tomonoriyamazaki/toytalker/docs/qwen3-tts-current-status.md

# ZakiCorp TTS（Qwen3-TTS）調査の経緯（2026-09-12〜13）

元実装の同時要求試験から、言葉の繰り返し・抜けの原因特定、バッチ推論エンジンの実装と本番反映までの経緯を時系列で残す。**現在の状態と設計・計測の詳細は [バッチエンジンの実装と検証](qwen3-tts-batch-engine-2026-09-12.md) を参照。** 本書は「なぜそうなったか」を追うための記録で、「今の結論」以下の各節はその時点の記述のまま残している。

各段階の個別メモ（同時要求結果・処理能力分析・区間計測・CUDAトレース・改善候補比較・可変チャンク・並列比較）は2026-09-13に本書と batch-engine へ要点を統合して削除した。生ログ・音声は `tts-models/faster-qwen3-tts/benchmarks/concurrency/results/`（Git対象外）にある。

## 今の結論

**改善版は1件ずつなら少し速くなり、確認した音声も問題なかった。しかし、4件同時では待ち時間・再生の途切れが残り、言葉の繰り返しや抜けも見つかった。複数人を快適に捌ける状態には、まだできていない。**

改善版は本番に適用していない。検証後に元のプログラム・設定へ戻し、音声生成と監視タスクの復帰を確認済み。現在は調査を停止しており、このまとめの作成中に追加の負荷試験は実行していない。

## 何を目指しているか

ToyTalkerを100人が使えるようにしたい。そのために、自前のRTX 5090＋Qwen3-TTSでどれだけ音声を生成できるか、改善の余地があるかを調べている。

「100人がサービスを利用する」ことと「100件が同時に音声生成を要求する」ことは同じ条件ではない。実際の会話頻度や返答の長さも必要だが、現段階では少人数の同時要求でも問題が残っている。100人対応は未達・未検証。

## ここまで何をしたか

| 段階 | やったこと | 分かったこと |
|---|---|---|
| 元の性能を測定 | 元のプログラムに1・2・4・8・16・32件の要求を同時に送った | 初期試験では1〜16件の総生成量がほぼ一定。要求数を増やすと待ちが長くなり、32件は大半が期限超過 |
| 時間の内訳を調査 | トークン生成・波形変換とCPU/GPUの処理時間を計測 | 最初の区間計測ではトークン生成約81%、波形変換約19%。GPUの性能限界そのものは未確定 |
| 小さな高速化を試行 | 重複トークン除去の変更、波形への変換間隔の調整 | 重複除去の変更は約1%の時間短縮。変換間隔を広げると処理量は増えるが、初回音声が遅くなった |
| 先頭を小さく保つ改善版を試行 | 先頭6チャンクは通常と同じにし、その後の変換間隔を広げた | 単独では処理量約7.2%増、初回音声は約0.079秒遅い。ユーザーが比較音声を聞き、違和感なしと確認 |
| 改善版の同時利用を比較 | 通常版と改善版で同時2件・4件を測った | 同時数を増やしても総生成量は増えず、改善版4件では待ち・模擬再生の途切れが残った。保存音声にも異常の報告あり |

## 元実装の分析で分かったこと（2026-09-12）

- **GPUへの入力は1要求分の形。** `api_server.py` は共有モデルの同期ジェネレーターを呼ぶだけで、推論ワーカーやバッチ受付はない。`talker_graph.py` の入出力バッファは `(1, 1, hidden_size)`。同時HTTP要求を増やしてもGPUへ渡すバッチ数は増えず、1〜16件で総生成倍率が約3.1倍で一定なのはこの構成による。
- **推論がイベントループを塞ぐ。** `generate_pcm()` はasyncジェネレーターだが内側の生成は同期処理。StarletteのStreamingResponseが自動で別スレッドへ移すのは同期Iterableだけで、asyncジェネレーターには適用されない。同時16件でHTTPヘッダー到着p95が29秒、32件で `/health` 無応答になったのはこの経路。バッチ版でHTTP側をQueue受け取りだけにしたのはこのため。
- **却下した案。** モデルを単純に複数スレッドから呼ぶ案は、共有CUDA graphとstatic cacheの状態を分離しないため採らない。複数プロセスで独立モデルを置く案は、GPUの取り合いで遅くなり得るのでVRAMの空きだけを理由に採用しない。1.7Bと0.6Bの比較は品質が許せる場合の別案として保留。
- **処理時間の内訳（単独要求）。** トークン生成81%、波形デコード19%、入力準備0.1%。波形デコードを半分にできても全体は約1.10倍、ゼロという非現実的な仮定でも約1.23倍にしかならず、チャンク調整路線では上限が低いと分かった。モデルが最初のチャンクを返すまで0.150秒に対しHTTPの初回PCM p50は0.743秒で、約0.6秒がAPIの1チャンク保留と同期推論中の通信待ち。バッチ版で初回PCMが0.25秒になったのはこの差が消えたため。
- **100人対応の換算。** 100人が各20秒に1回、約8秒の返答を要求すると約40音声秒/実時間秒が必要。元実装の約3.1倍とは約13倍の差。仮定による感度分析で、実際の利用割合・返答長で変わる。

## 「並列テスト」という説明について

**複数の要求を同時に送る試験は、最初から行っている。今回が初めてではない。**

今回作ったのは、音声への変換回数を減らす改善版。複数人分を効率よくGPUで同時に計算する仕組みを新しく実装したわけではない。

実測で言えるのは「要求数を増やしても、全体の音声生成量が増えていない」ということ。内部が完全な直列処理なのか、途中で交互に動いているのかを、この結果だけで決めつけない。以前の説明では「同時要求の試験」と「並列化の実装」を混同させてしまった。

## 改善版の最新結果

| 条件 | 結果 |
|---|---|
| 単独 | 通常比で処理量約7.2%増。初回音声0.748秒→0.827秒。保存した比較音声はユーザー確認で問題なし |
| 同時2件 | 総生成倍率3.40倍。初回音声p95は2.34秒。10/10受信完了、模擬再生の途切れ0/10 |
| 同時4件 | 総生成倍率3.31倍。初回音声p95は4.05秒。20/20受信完了だが、模擬再生の途切れ20/20。聴取した先頭4音声のうち2つに異常 |

「生成倍率3.40倍」は、実時間1秒あたり合計約3.40秒分の音声を生成できたという意味。対応人数を表す数値ではない。2件から4件へ増やしても、この総量は増えなかった。

模擬再生の途切れは、受信時刻から計算した推定。実機スピーカーの音を直接測った結果ではない。また、受信完了は音声内容の正常性を保証しない。完成WAVを再生しても、通信中の待ち時間や途切れはそのまま再現されない。

## 見つかった音声の問題

対象フォルダ:

```text
C:\Users\exodj\projects\tts-models\faster-qwen3-tts\benchmarks\concurrency\results\20260912T125241_468029Z
```

| ファイル | ユーザーによる確認 |
|---|---|
| `measure-000-00.wav` | 言葉の繰り返し、飛ぶ・抜けるような感じがある |
| `measure-000-01.wav` | 言葉の繰り返し、飛ぶ・抜けるような感じがある |
| `measure-000-02.wav` | 問題なし |
| `measure-000-03.wav` | 問題なし |

00・01について、声の崩れやノイズはないとの報告。症状の正確な位置や、どの語が抜けたかまでは未確認。

**原因は未確定。** 元のプログラムにもある同時生成の問題なのか、今回の改善が原因なのかは分かっていない。共有キャッシュ等への干渉は調査候補だが、原因と断定していない。先頭4音声の結果から全20件の品質や不良率も判断しない。

## 次にすること

まず、保存済みの「通常版・4件同時」の音声を聞き、同じ繰り返し・抜けがあるか比較する。追加の負荷試験やサービス停止は不要。

```text
C:\Users\exodj\projects\tts-models\faster-qwen3-tts\benchmarks\concurrency\results\20260912T125417_081918Z
```

対象は `measure-000-00.wav` 〜 `measure-000-03.wav`。これは原因を絞る手掛かりで、この4つだけで原因が確定するわけではない。

その結果を踏まえて、同時生成中の状態が混ざっていないか、改善部分に問題がないかを調べる。処理量を大きく増やすには、その後に独立した要求状態を持つ推論方式などの比較が必要。これらの追加調査・実装はまだ実行していない。

**今の作業状態：まとめの作成まで完了。負荷試験は停止中。本番は元の設定。次のユーザー作業は、上記の通常版4音声の聴取。**

## 追記（2026-09-12 夜）：原因の特定とバッチ推論の見込み

コードとログの再分析で、繰り返し・抜けの有力原因を特定した。推論グラフのKVキャッシュ（`talker_graph.py` の `StaticCache`）がサーバーに1つしかなく、同時要求が交互に進むたびに `prefill_kv` のリセットと各ステップの書き込みで互いの文脈を上書きする。生成済みトークン・テキスト供給・波形復号は要求ごとに独立しているため、声は崩れず文脈だけが混ざる。可変チャンク改善版の問題ではなく、元の実装の構造。同一文・同一話者の試験では症状が確率的にしか出ないが、本番のように文と話者が異なる要求が重なると露骨に出るはず。改善版4件の「音声総量37%増」は、41文字に54.88秒を生成した1件の暴走が主因。切り替えは送信バッファが約64KB（約1.6秒分）を超えた時点で起きており、チャンク境界ごとではない。

同時要求で総処理量が増えないのも同じ構造（1件分のバッチ固定グラフを時分割）による。

実装前の見込み計測として、talker・予測器・波形デコーダーをバッチNで動かした結果、1ステップはN=1の19.9msに対しN=8で27.9ms、N=16で38.3ms。4ステップ＋復号の見込みで総音声生成倍率はN=4で約10.8倍、N=8で約18.4倍、N=16で約25.2倍（現行約3.1倍）。詳細は [バッチエンジンの実装と検証](qwen3-tts-batch-engine-2026-09-12.md) の「設計の根拠となった事前計測」。

次の順は、(1) 別文・別話者を交互に進める再現試験で相互上書きを確定、(2) 音声認識による本文照合を性能計測へ組み込む、(3) 暫定で生成を1本の推論スレッドへ直列化、(4) 要求ごとに独立KV領域を持つバッチ推論の実装と2/4/8件の実測。本番の共有キャッシュ問題は未対策。

## 追記（2026-09-12 深夜）：バッチ推論エンジンの実装完了

上記(4)を実装し、HTTP経由で検証した（[実装と検証](qwen3-tts-batch-engine-2026-09-12.md)）。同時16件で総音声生成倍率20.95倍・初回PCM p95 0.84秒・模擬再生枯渇0/48（現行は3.12倍・33.6秒・全件枯渇）。同時4件で9.42倍・初回p95 0.42秒。単独でも初回PCMが0.75秒→0.25秒。隠れ状態は元実装とbf16の1〜2ulp以内で一致。別話者8件同時も全件完了。

**本番は未適用（元の `api_server.py` のまま）。** 適用前に、保存音声の聴取、音声認識による本文照合、切断・長時間運用の確認が必要。対象ファイルは `tts-models/faster-qwen3-tts/batch_engine.py`、`api_server_batch.py`。

## 追記（2026-09-13）：本番へ適用

ユーザーが保存音声を聴取し、同一文8件・別話者8件とも問題なしと確認（`measure-000-06` の末尾切れは旧実装にも同じ形で存在する生成側のEOS判定で、並列とは無関係）。ユーザー指示により10:27に本番をバッチ版へ切り替えた。手順と復旧は [起動・復旧](tts-boot-recovery.md) の「APIの版の切り替え」、結果は [実装と検証](qwen3-tts-batch-engine-2026-09-12.md) の本番節を参照。

**今の作業状態：本番はバッチ版（`api_server_batch.py`）で稼働中。ngrok経由の同時1/4/8件・別話者8件は受信成功・枯渇0。次のユーザー作業は、スマホ/ESP32からの実会話で音声を確認すること。**

## 追記（2026-09-13 昼）：第2版を本番反映

ユーザーがアプリで会話を確認（問題なし、速くなった体感）。その後、本番で同時16件・切断試験を確認し、cache長1024・波形復号のCUDA graph・同時32件・長文の文末分割を実装して12:06に本番へ反映した。8001番の測定は同時32件で33.0倍（第1版16件で20.95倍）。詳細は [実装と検証](qwen3-tts-batch-engine-2026-09-12.md) の第2版節。

**今の作業状態：本番は第2版で稼働中。次のユーザー作業は、通常会話と長文の読み上げ（分割境界の聞こえ方）の確認。**

## 詳細記録

- [元実装の1〜32件測定](qwen3-tts-capacity-2026-09-12.md) — バッチ版の改善幅の比較対象
- [バッチエンジンの実装と検証](qwen3-tts-batch-engine-2026-09-12.md) — 現行本番版。事前計測（見込み計測・CUDAトレース・改善候補比較）もここに統合
