tomonoriyamazaki/toytalker/docs/device-audio-investigation-2026-09-11.md

# 2026-09-11 デバイスの音途切れ報告・初回調査

## 調査対象と結論

中島さんからの「デバイスと会話できたが、会話が途切れ途切れになる。Wi-Fi環境は良い」という報告を受け、CloudWatchと対象候補のDynamoDB登録情報を読み取り調査した。設定変更・デプロイ・ファーム変更は行っていない。

報告に近い時間帯に、デバイス `90:da:72:49:ba:e1` の会話要求7回を確認。TTSは **Sakura / zundamon**、LLMは **Google / gemini-2.5-flash**。ElevenLabsの同時実行制限を今回の原因とする根拠はない。

ただし、このIDが中島さんへ渡した実機と一致するかは確認待ち。実機ファームのバージョンも未確認。

1回の返答には、短い先行音声の後、Web検索などで次の音声送信が遅れる区間がある。他の返答はサーバー側では比較的速く音声を送信しており、この1件だけで報告全体の音途切れを説明できない。端末の受信・再生状況はCloudWatchだけでは確認できていない。

## 時刻の整理

- 提供画像 `IMG_1195.PNG` のメッセージ表示は **Today 12:21 AM**。0:30ではなく0:21。
- 撮影日が9/11、表示タイムゾーンが日本時間なら、2026-09-11 00:21 JST。画像の表示だけでは日付・タイムゾーンは確定しない。
- 初回ログ調査範囲: **2026-09-11 00:00〜01:00 JST**（UTC 2026-09-10 15:00〜16:00）。
- 送信者の滞在場所は、受信側画面の時刻からは判断しない。

## 調査したデータ

AWSリージョン: `ap-northeast-1`

CloudWatchロググループ:

- `/aws/lambda/toytalk-api-stream-for-esp32-lambda`
- `/aws/lambda/toytalker-backchannel-for-esp32-lambda`
- `/aws/lambda/toytalk-soniox-stt-lambda`
- `/aws/lambda/toytalker-device-setting-lambda`

DynamoDB: `toytalker-devices` の対象候補1件を取得。デバイスID、名前、作成時刻、最終更新時刻、キャラクターID、ファームバージョン属性に限定。

- `created_at`: 2026-09-06T00:59:44.590Z
- `last_seen`: 2026-09-10T15:17:02.258Z（9/11 00:17:02 JST）
- `character_id`: `default`
- `device_name`: 空欄
- `firmware_version`: 取得結果に属性なし

`last_seen`は今回のデバイス登録APIの時刻と一致する。ローカル実装では登録時や設定更新時にも更新されるため、最終会話時刻や常時接続の生存確認値とは扱わない。

## 観測結果

00:17:02 JSTにデバイス登録API呼び出しと対象IDの設定取得があり、その後、次の7件の本文要求があった。

音声秒数はログのPCMバイト数を、実装前提の24kHz・16bit・mono（48,000 bytes/秒）で換算したもの。実際のスピーカー再生時間を測った値ではなく、端末が挿入する無音も含まない。

| 本文要求開始 JST | Lambda所要時間 | 最初の音声送信ログまで | 音声ブロック数 | 合計音声相当時間 |
|---|---:|---:|---:|---:|
| 00:17:15.236 | 1.939秒 | 1.694秒 | 2 | 3.803秒 |
| 00:17:42.069 | 4.444秒 | 1.183秒 | 2 | 9.608秒 |
| 00:22:12.189 | 1.259秒 | 1.224秒 | 1 | 1.212秒 |
| 00:22:46.301 | 1.481秒 | 1.452秒 | 1 | 2.757秒 |
| 00:23:00.929 | 2.608秒 | 1.139秒 | 3 | 5.458秒 |
| 00:23:19.362 | 1.404秒 | 1.240秒 | 2 | 5.760秒 |
| 00:23:35.049 | 1.446秒 | 1.152秒 | 3 | 8.338秒 |

7件ともPCM生成・送信処理のログとLambdaのEND/REPORTがある。取得範囲に明示的な例外・タイムアウトのログは見つからなかった。ただし、クライアントへ返すエラーが必ずCloudWatchへ出るとは限らないため、END/REPORTだけで全処理成功や端末再生成功を証明しない。

相槌ログには00:23:16.840 JSTに「音が途切れるね」という入力断片がある。報告との関連を示す手掛かりだが、相槌ログ自体にはデバイスIDがなく、時刻による相関である。

Soniox用Lambdaで確認できるのは一時キー発行側の処理。音声認識のWebSocketは端末からSonioxへ直接接続するため、その切断・音声送信間隔をこれらのLambdaログから追うことはできない。

## 音声間の空白候補: 00:17:42の返答

Request ID: `7a68104e-f55d-42df-a706-d03d68bb1220`

| イベント | JST |
|---|---|
| Lambda START | 00:17:42.069 |
| 音声1送信ログ: 58,002 bytes、約1.208秒分 | 00:17:43.252 |
| Web検索開始 | 00:17:43.253 |
| Web検索結果取得 | 00:17:45.192 |
| 音声2送信ログ: 403,164 bytes、約8.399秒分 | 00:17:46.481 |
| Lambda END | 00:17:46.513前後（REPORT所要時間4.444秒） |

先頭音声と次の音声の送信ログ間隔は **3.229秒**。このうち検索要求〜結果取得は **1.939秒**。先頭音声は約1.208秒なので、先頭をすぐに再生する仮定なら、次の音声が出るまで約2.02秒の不足が生じ得る。

これは実測の無音長ではない。相槌、端末の初期バッファ、受信遅延、再生開始時刻で実際の空白は変わる。また3.229秒をすべてTTS待ちと解釈しない。検索・検索後のLLM出力・TTS・送信処理を含む。

検索対象はシアトルの天気だったが、話題から物理的な滞在場所を確定しない。今回取得したログには、所在地を判定できる送信元IP情報は確認できなかった。

## 残る候補と確認方法

| 候補 | 根拠と限界 | 次の確認 |
|---|---|---|
| 短い先行音声の後で検索待ち | 上記1件で送信間隔に不足候補あり | 検索なしの返答でも同じ症状か比較 |
| 文ごとの意図的な間 | ローカルv0.5/v0.6/v0.7には`TTS_SEGMENT_GAP_MS = 400`がある | 実機の版を確認し、文間の間なのか単語途中の音切れなのかを区別。v0.4へ同じ設定を当てはめない |
| 端末受信・再生バッファの枯渇 | サーバーが早く送れている返答でも、ネットワークや端末処理による遅れは残り得る | `[PLAYER] underrun`、`[STATS] underruns`、受信・I2Sログ。Wi-Fi電波が良いだけでは通信経路全体の安定性は分からない |
| 音声認識や発話区切りの問題 | 「会話が途切れる」が返答音声だけを指すか未確定 | 入力認識の途切れと出力再生の途切れを区別 |
| 実機ファーム固有の問題 | 実機の版が不明 | 配布時の版・設定を確認。手元のv0.7のAEC等を原因と決めつけない |

端末の再生ログは現在確認したCloudWatchデータには含まれない。シリアルログ取得が難しい場合は、まず短い録画で「文と文の間」「単語の途中」「返答までの待ち」のどれかを切り分ける。その後、必要なら遠隔診断データの送信を別の実装として検討する。

## 次に進む順序

1. 対象IDが中島さんの端末と一致するか、配布ファームの版を確認する。
2. 検索なし・短い返答で症状が出るかを確認する。
3. 端末の受信・バッファ枯渇・再生時刻と、CloudWatchのRequest ID/時刻を対応づける。
4. 原因の所在を絞ってから、文間の間、検索時の応答設計、バッファや送信方式の変更を検討する。

## DynamoDB会話履歴との照合（同日追記）

ユーザーから追加依頼を受け、現在の`owner_id`と対象デバイスIDの組み合わせをパーティションキーとして`toytalker-chat-logs`をQueryした。期間はUTC 2026-09-10 14:00〜16:00（JST 23:00〜翌01:00）。14レコードを評価し、14レコードが該当した。すべて`source=esp`、セッション`1280-470114`の7往復。現在の所有者との組み合わせについての結果であり、過去の別所有者に紐づく履歴まで調べたものではない。

### ユーザー入力の記録

以下は保存された音声認識テキスト。元の発声音声との照合はできておらず、不自然な文字列を本人の発言どおりと断定しない。

| JST | 保存されたユーザー入力 |
|---|---|
| 00:17:15.260 | こんにちは。 |
| 00:17:42.073 | えっと、今日のシアトルの天気を調べたい。 |
| 00:22:12.192 | ズームに行くか、頑張って。 |
| 00:22:46.305 | こちらよくある質問なんですけど。 |
| 00:23:00.931 | これが枕に入れるデバイスで、 |
| 00:23:19.365 | 音が途切れるね。 |
| 00:23:35.052 | キロッパ |

「枕に入れるデバイス」「音が途切れるね」が対象デバイスの本文履歴にもあるため、相槌ログの時刻相関だけだった初回調査より、報告との対応が強まった。氏名による本人確認には至っていない。

00:23:00の入力に対する返答は「枕に入れるデバイスですね！面白そう！それは何をするものなのですか？」。00:23:19の入力に対しては「ごめんなさい、音が途切れてしまいましたか。もう一度お話しいただけますか？」と返答している。後者はユーザー入力に応じたLLMの発言で、システムが音切れを検出した診断ログではない。

### 保存テキストの重複と実際の音声送信の違い

天気の返答はDynamoDB上で「調べてみるね。調べてみるね。」と先頭が重複している。しかし、CloudWatchの音声送信ログは次の2ブロックのみ。

1. 「調べてみるね。」
2. 天気の回答本文

ローカル実装の`emitSegment`には直前の同一文を再送しない処理があり、このログと整合する。**履歴の重複は確認できるが、同じ音声を2回再生した証拠ではない。** テキストの保存経路と音声化経路の差を、別の課題として扱う。

### 設定・利用集計

- 現在のデバイス設定は`character_id=default`。当時のCloudWatchには`hasPersonality=false`があり、独自の人格設定を読み込んだ形跡はない。一般的なシステムプロンプトがないという意味ではない。
- 取得したデバイスレコードには`backchannel_enabled`属性がない。ローカルのキー発行実装では未指定時は有効扱い。実際に同時間帯の相槌生成も観測されている。
- `owner_id`はアプリが生成・保持する`u_`付きUUID。確認したアプリ実装では氏名から生成するIDではなく、取得レコードにも氏名・所在地はない。この値だけで本人や滞在地を特定できない。
- 対象端末の9月利用集計にはUTC日付9/10のLLM/STT/TTSレコードが各1件あり、各`requests=7`。本文TTS文字数は208文字。これは利用集計の加算回数であり、TTSの実HTTPリクエスト数7件という意味ではない。CloudWatchの本文音声ブロックは合計14件。
- 記録上の合計金額は約0.8296円（LLM約0.6640円、STT約0.0720円、TTS約0.0936円）。内部設定のマージン1.5等を含む計算値であり、プロバイダー請求額・AWS費用・相槌も含めた総原価としては使わない。今回、料金設定の妥当性は検証していない。

登録時刻9/6は既存レコードの作成時刻。9/11の登録処理では所有者が更新され得るため、9/6から同じ人が使用していたとは断定しない。

参照: [所有者ID生成](../app/hooks/useOwnerId.ts)、[会話履歴保存・利用集計](../backend/toytalk-api-stream-for-esp32-lambda/index.mjs)

## 手元端末ba:e5との比較（同日10:13〜10:14 JST）

ユーザーが手元の端末で試し「全く問題なく動いた」と報告。CloudWatchで`90:da:72:49:ba:e5`の4要求を確認し、DynamoDBの同一セッション`1471-645527`の4往復と照合した。履歴にも「まあ、特に問題ないように見えますね。」という入力がある。

### 条件の比較

| 項目 | ba:e1（報告対象候補） | ba:e5（手元） |
|---|---|---|
| 観測時間 JST | 00:17〜00:23 | 10:13〜10:14 |
| 使用Lambda | ESP32用本文Lambda | 同じ |
| TTS / voice | Sakura / zundamon | 同じ |
| LLM | Google / gemini-2.5-flash | 同じ |
| キャラクター | default、人格設定なし | ユーザー作成キャラ、人格設定あり |
| 相槌 | 同時間帯に生成あり | 同時間帯に生成あり |
| デバイス名 | 空欄 | v0.2 大スピーカー |
| ファームバージョン属性 | なし | なし |
| 再生状態 | 途切れるとの報告候補 | 問題なしとのユーザー報告 |

**「v0.2 大スピーカー」は登録名であり、実機ファームがv0.2であることの証明ではない。** 両端末の実際のファーム・基板・音響配置・通信環境が同一かは未確認。

本文Lambdaの取得時点の`LastModified`は2026-09-10T10:16:47Z（JST 19:16:47）で、両方の観測時刻より前。間のLambda更新で今回の差が出たことを示す情報はない。現在のコードハッシュは`nmsHU9spd2U08fsJ4fg20/MWAuvjpnCJLMbZ3F2r+Ks=`。設定テーブルや外部サービスの時間帯による変化まで同じと証明したものではない。

### 手元の4要求

| 開始 JST | 内容の概要 | Lambda所要時間 | 最初の音声送信まで | ブロック数 | 音声相当時間 |
|---|---|---:|---:|---:|---:|
| 10:13:54.439 | 声が聞こえるか確認 | 1.694秒 | 1.484秒 | 2 | 2.353秒 |
| 10:14:07.118 | シアトルの天気 | 5.575秒 | 1.891秒 | 2 | 6.258秒 |
| 10:14:33.715 | 問題ないとの発話 | 1.473秒 | 1.301秒 | 2 | 4.931秒 |
| 10:14:43.982 | 東京の天気 | 4.955秒 | 1.215秒 | 3 | 10.629秒 |

時刻・所要時間はCloudWatchのSTART、音声送信ログ、REPORTに基づく。DynamoDBの`duration_ms`とは計測範囲が少し異なるため混ぜて集計しない。端末への到着・再生時刻ではない。

### 同じシアトル天気検索の比較

| 指標 | ba:e1 | ba:e5 |
|---|---:|---:|
| Lambda全体 | 4.444秒 | 5.575秒 |
| 最初の音声送信まで | 1.183秒 | 1.891秒 |
| 最初の音声の長さ相当 | 1.208秒 | 1.327秒 |
| 音声1→音声2の送信ログ間隔 | 3.229秒 | 3.655秒 |
| Web検索時間 | 1.939秒 | 1.674秒 |

ba:e5のRequest ID: `005246ed-712d-4458-ab0d-0389c7c1291e`。

**問題なく聞けた手元のほうが、サーバー全体時間も音声ブロック間隔も長い。** よって「ba:e1だけLambdaが遅かった」という説明はこの比較からは支持されない。短い先行音声の後に検索待ちがあること自体は両方で観測されるため、ba:e1固有の症状の原因と確定しない。

同じ話題でも人格設定・返答の長さ・時刻が異なるため、完全な同条件試験ではない。手元で問題なく聞けた理由を、バッファ量やネットワークだけに決めつけない。次は以下を優先する。

1. 相手の「途切れる」が検索待ち・文間の間・単語途中の音切れのどれかを確認。
2. 配布したファームと手元ファームの版・再生設定を照合。
3. 可能なら同じdefaultキャラクター、ずんだもん、検索なしの短い質問で比較。
4. 端末の受信・アンダーラン記録を取得し、CloudWatchの送信ログと突き合わせる。

手元の天気履歴にも前置きの重複があるが、音声送信では1回のみ。これはba:e1固有の問題ではない。

## 実装参照（一覧）

- [本文Lambda](../backend/toytalk-api-stream-for-esp32-lambda/index.mjs): `ttsBufferSakura`、`sendPCM`、`emitSegment`、Web検索処理
- [デバイス設定Lambda](../backend/toytalker-device-setting-lambda/index.mjs): デバイス登録・`last_seen`更新
- [Sonioxキー発行Lambda](../backend/toytalk-soniox-stt-lambda/index.mjs)
- [v0.5再生終了の既存調査](esp32-playback-end-timing.md)
- [v0.7本文開始の高速化で保留した候補](deferred-items.md)

実装に関する説明はローカルソースを参照。本番コードのダウンロード・差分照合は未実施。
