tomonoriyamazaki/toytalker/docs/esp32-v07-aec.md

# v0.7 AEC音声介入実験版（2026-09-10）

AECの変更を独立して検証し、音量方式へ戻せるよう、Arduinoスケッチをバージョンごとに保持する。

19:02の本文開始ログを受けた高速化候補のうち保留した分は [先送り項目](deferred-items.md) を参照。保存点 `d3a59a8` を基準に、相槌の前置き重複を減らす通知修正だけを実装した。相槌取得の並行化と本文プリバッファの変更は行っていない。

## 最新状況（2026-09-10、20:09以降の追加試験を反映）

- ユーザーが現状を次の開発の基準として受け入れ、`9925fe0` までをローカル `main` へ統合するよう依頼。ほかの改修は統合後の `main` から進められる。以下の配置依存や未確認項目は既知の制約として残し、今回のマージを追加試験待ちにはしない。
- 声による停止・通常再生・本文開始速度は改善報告あり。ただし、未固定のスピーカーをマイクへ向けると意図しない停止が起きることをユーザーが確認した。机上・手持ち静止・再生途中の持ち上げ自体は、今回の比較では問題なし。
- AECを追加調整する場合は、スピーカーとマイクを実際に使う位置・向きに固定して評価する。AECの再適応中だけの問題か、向けた状態でも消し残るのかは未確認。詳細は末尾寄りの「スピーカーの向きを変えた追加試験」を参照。
- AECは自動停止ON、毎ターン再初期化ON、NLP強度NORMAL。抑制強度・参照の整列・割り込み条件の調整余地はあるが、追加試験後の設定変更はしていない。強く抑えるほど人の声も弱め得るため、声への反応と誤停止を両方比較する。
- AECの保存点は `d3a59a8`。その後の②相槌通知修正はビルド済みで、今回の引き継ぎ記録と合わせて保存する。実機の通知値と効果の対応は確認途中。①相槌取得と本文要求の並行化は保留、③本文プリバッファ32KBは維持。ユーザーが別途変更したLambdaプロンプトは `87035d8` でコミット済み。保存内容・コミット名は [CLAUDE.mdの引き継ぎ記録](../CLAUDE.md) を参照し、再開時の状態は `git status` / `git log` で確認する。
- スマホから音声割り込み・相槌を再起動なしでON/OFFする案も相談した。まだ未実装で、今のファームが会話中に設定を同期するわけではない。[現状と設定同期の候補](esp32-ota-settings-plan.md) を参照。

| バージョン | 役割 | 現在の状態 |
| --- | --- | --- |
| [v0.5](../devices/mcu/esp32_s3/toytalker_mini_v0.5/toytalker_mini_v0.5.ino) | 安定版 | 従来の会話・ボタン割り込み。変更しない |
| [v0.6](../devices/mcu/esp32_s3/toytalker_mini_v0.6/toytalker_mini_v0.6.ino) | 音量方式の検証版 | 再生中のマイク監視と音量集計あり。自動停止OFF。調整余地を残す |
| [v0.7](../devices/mcu/esp32_s3/toytalker_mini_v0.7/toytalker_mini_v0.7.ino) | AECの開発版 | 毎ターン再初期化後に改善報告。追加試験では持ち上げ自体は問題なく、未固定スピーカーをマイクへ向けると停止。配置を固定して残る問題を評価する。本文の相槌通知修正も実機評価中 |

## 引き継いだ状態

v0.7の作成時はv0.6のスケッチと4つのヘッダーを独立したファイルとして複製した。Arduino IDEの個人設定はコピーしていない。v0.7からv0.6のヘッダーを参照しないので、AEC開発でv0.6の動作が変わることを避けられる。

- `VOICE_BARGE_DETECT_ONLY=true`。AEC未使用・初期化失敗時の生マイクは音量検出ログのみで、自動停止しない。AECの停止設定は別の `AEC_BARGE_DETECT_ONLY`。
- 生マイク比較用のRMS閾値3,200、保持120ms、ウォームアップ500msを継承。AEC処理後の判定には別の閾値・保持時間を使う。
- `VoiceRxTestMode::MonitorResetEachTurn`。再生中もマイクを動かし、再生後にRXを解放、次の録音で再確保する。
- TTSセグメント間400ms、受信処理、音量・メモリ・切替時間の計測、ボタン割り込みを継承。
- 現時点の起動表示は `ToyTalker Mini v0.7 (AEC barge-in trial)`。初期化に成功した場合だけ `[AEC] ready=1` が出る。

v0.6の10ターン連続会話、音量方式での検出→録音復帰69ms / 36ms、再生音による誤停止等は [v0.6の実機記録](esp32-v06-voice-barge-in.md) にある。これらはv0.7やAECを実機確認した結果ではない。

## 今回の実装

`AecMonitor.h` の `AEC_ENABLED=true`。Espressifの `AEC_MODE_FD_LOW_COST` / NLP `NORMAL` / filter length 4を使用する。モデル用パーティションは追加していない。AEC後のRMSを自動停止の条件に使う。AEC後の音声をSonioxへ送る実装や、停止前の発声を録音へ引き継ぐ実装はまだない。停止後は通常STTに戻り、ボタンでの停止も継続する。

### 再生参照とI2S

v0.7のみ `driver/i2s.h` のlegacy APIから、同じインストール済みコアの `driver/i2s_std.h` へ変更した。新旧ドライバは混在させない。ネットワーク到着時やDMAコピー時のPCMではなく、TXの `on_sent` callbackで、送信を終えたDMAバッファを取り出すための変更。

- マイク: I2S0、16kHz、32bit、左slot、RX DMA 4×512。再生後のRX解放・次回STTでの再確保を継続。
- 再生: I2S1、24kHz、stereo 16bit、TX DMA 8×1023。従来の実サイズ4092 bytesを明示した。ピン、再生音量、区切り400msは継承。
- TXは `auto_clear_after_cb=true` / `auto_clear_before_cb=false`。ゲイン・クリップ後の送信波形をクリア前に取得し、再生データが来ない区間はクリアされた無音も取得する。相槌・本文・区切り無音・末尾flushが同じ経路になる。
- RXの `on_recv` とTXの `on_sent` でDMA完了時刻を記録。これはデジタル転送の完了時刻であり、スピーカーの音響遅延を直接測っているわけではない。
- 従来の `[DMA_TAIL]` は新APIのDMAサイズ・キュー溢れカウンターへ接続した。ドライバ変更後の実機での終了時間は再確認する。

### 参照の整列と評価

参照には24kHzの25タップローパスフィルター（7kHz cutoff）をかけてから、16kHzのマイク時刻へ線形補間する。フィルターの0.5msの群遅延を参照時刻に反映する。DMAサンプル数に沿った時計を使い、IRQ時刻の揺れへ毎フレーム追従せず、小さく補正する。連番欠落や3msを超える時刻差は不連続として扱う。

`AEC_REFERENCE_ADVANCE_MS=16` は、参照をマイクより先の時刻から与えてAECフィルターに因果的な余裕を持たせる試験値。物理的なエコー遅延の実測値ではない。必要な最後の参照サンプル（補間相手を含む）が到着したら、512 samples / 32msのマイクフレームを処理する。未到着なら最大96ms待つ。処理前に全512サンプルを検証し、参照が不足・欠落・上書き済みならそのフレームを評価せず、連続音量窓も切る。参照不足を無音として成功扱いにはしない。

初版は一律96ms待っていたが、01:36の実機結果を受けて到着時点で処理できるよう変更した。起動ログは `max_ref_wait_ms=96`。実際の待ち時間はDMA完了・参照時刻・タスク実行タイミングに依存する。最初の非ゼロTX波形が届く前は検出が未有効なのでAEC演算を省き、接続・受信へCPU時間を残す。**再生終了→STT再開時は保留音声を捨て、その消化を待たない。** 処理中の1フレームとタスク停止通知を待つ時間は残る。未処理の末尾はサマリに含まれず、`held_discarded` に保留枚数を出す。

マイクはSPH0645のDCを除去して16bitへ飽和変換する。v0.6の20msごとの分散RMSと厳密に同じ尺度ではない。AEC用の持続値は32ms×4枚=128msの窓で、v0.6の120ms値からそのまま閾値を移さない。各ターンの参照履歴・時計・音量統計は初期化し、最初の再生音から500msは統計のウォームアップにする。AEC本体は従来起動時に一度確保して再利用していたが、18:26の結果を受け、現在は `AEC_RESET_EACH_TURN=true` で2ターン目以降に本体だけを破棄・再作成する比較版。初回は起動時の未使用インスタンスを使う。小さな受渡しキュー・参照履歴・PCM作業バッファは再利用する。

### メモリと失敗時

インストール済みSDKは `CONFIG_I2S_ISR_IRAM_SAFE=1`。ISRの小さな受渡しキューは内部SRAMに置き、履歴・遅延マイク音声はPSRAMに置く。ISR内でPSRAM、音声処理、ヒープ確保、ログ出力へ触れない。ISRとタスクの共有カウンターは短いESP-IDF critical sectionで保護し、データのコピー中はロックしない。このツールチェーンの `std::atomic<uint32_t>` は常時lock-freeではないため、ISRでは使わない。

AECの状態領域はPSRAMを指定し、APIへ渡す3つの512-sampleバッファは16-byte境界の内部RAM。監視タスクのスタックは4KB→8KB。ISR受渡しを含む `aecMonitor` は約8.4KBの静的内部RAMを使用する。静的RAMのビルド表示と、AEC内部の実行時確保・TLS等の動的確保は別々に評価する。

AEC初期化やバッファ確保に失敗した場合は確保分を解放し、音量計測だけへ戻る。その場合も自動停止はOFF。再生タスクの確保失敗も検出し、リングを使用せず直接再生へ戻る。TLSアロケーターは計測版ではコア標準だったが、01:20の接続失敗を受け、現在は以下のPSRAM固定に変更した。

### TLS作業メモリのPSRAM移行

`TlsMemory.h` の `TLS_PSRAM_ENABLED=true`。起動時、WiFi接続・HTTPS・WSS・AEC初期化より前に一度だけ `mbedtls_platform_set_calloc_free()` を設定し、mbedTLSのcallocを `MALLOC_CAP_SPIRAM | MALLOC_CAP_8BIT` へ固定する。Lambda・Soniox・相槌HTTPSに共通で効く。設定は接続中に変更せず、PSRAM確保失敗時に内部RAMへは戻さない。サイズの乗算オーバーフローを拒否し、freeは元の内部RAM割り当ても扱える `heap_caps_free()` を使う。DMA・ISR・タスクスタックの確保先は変更していない。

Arduino 3.3.11 / IDF 5.5.5のローカルSDKで `CONFIG_MBEDTLS_INTERNAL_MEM_ALLOC=1`、`MBEDTLS_PLATFORM_MEMORY`、実行時アロケーター設定APIを確認した。[Espressifの実装](https://github.com/espressif/esp-idf/blob/v5.5.5/components/mbedtls/port/esp_mem.c) も、内部RAM指定とPSRAM指定のcallocを別の構成として持つ。スケッチ内でSDK設定マクロを書き換える方式は使わない。

起動時にmbedTLS公開callocで20,000 bytesを確保し、外部RAMであることと全ゼロを検査して解放する。`[TLS_MEM] allocator=psram ready=1 ... external=1 zeroed=1` が成功ログ。PSRAMがない・API設定失敗・プローブ不一致なら、アンプOFFでネットワーク接続前に起動を止める。`[BUILD] arduino=... idf=...` も記録する。

`[TLS_MEM]` の `calls / fail / largest_req` は起動プローブを含む累積確保呼び出し数・失敗数・最大要求。現在の使用バイト数ではない。`psram_free / psram_max_blk` と内部RAMの `[HEAP_CHECK]` を同じ接続段階で比較する。前回よりRAMが減っただけでリークと断定しない。音声リングとAECとTLSがPSRAMを共有するので、実機で連続会話・接続時間・音切れ・AECの欠落も確認する。

APIの出発点は [Espressif公式AEC](https://docs.espressif.com/projects/esp-sr/en/latest/esp32s3/acoustic_echo_cancellation/README.html)。手元のSDKには `esp_aec.h` と `libespressif__esp-sr.a` があり、`aec_create_from_config` / `aec_get_chunksize` / `aec_process` / `aec_destroy` をモデル領域なしで単体リンクできた。実装ではローカルのAPI仕様を確認する。Arduino IDE、Flash 4MB、QSPI PSRAM 2MBを維持し、ESP-IDFやPlatformIOへの移行は行わない。

DMA callbackとauto-clearの順序は [ESP-IDF v5.5.4のI2S実装](https://github.com/espressif/esp-idf/blob/v5.5.4/components/esp_driver_i2s/i2s_common.c) も確認した。

## 現在の音声介入試験

`AecBargeGate.h` の `AEC_BARGE_DETECT_ONLY=false` で自動停止を試す。判定はAEC出力のRMSが1,200以上で、512 samples × 4フレーム = 128ms連続すること。最初の実際の再生音（相槌を含む）から500msは判定しない。閾値は交互試験の再生のみ789〜832と介入あり1,660〜1,720の間に置く仮の値で、初回の弱い介入1,123を検出できる設定ではない。

同じ候補4フレームの入力・出力エネルギーを比較し、AEC出力のRMSがマイク入力の25%以上残っていることも条件にする。1フレームだけの比率や、別時刻のターン最大値は比較しない。比率で却下した後も窓を更新するので、後から声を重ねれば再び候補になる。これは無発声での誤検出を受けた試験値であり、人の声を識別する機能ではない。再生音に埋もれた小さな声も却下する可能性がある。

入力変換で飽和したフレーム、未ウォームアップ、評価時点で音声が200msより古い場合は候補をリセットする。飽和後は新鮮で飽和のない8フレーム（256ms分）を評価対象から外し、その後に128msの候補を新しく作る。参照不足・マイクの不連続で候補を切っても、この保護は消さない。再度の飽和で保護を延長し、次ターン開始で全状態をリセットする。通常の声で飽和しなければ、この待ちは追加されない。1ターン1回だけ発火する。飽和しない接触音や再生音の残りで誤停止する可能性は残る。

発火時は監視タスクでアンプをOFFにしてから既存の割り込みフラグを立て、captureを止める。ソケット・再生タスク・I2Sドライバの終了は従来のボタン割り込みと共通の処理で行い、通常STTへ復帰する。AEC初期化失敗時は生マイクの計測のみとなり、自動停止しない。

1. v0.7を書き込み、`[AEC] ready=1` と `detect_only=0 barge_rms=1200 barge_hold_ms=128 min_retained_pct=25 clip_recovery_ms=256` を確認する。
2. 端末を置いたまま触らず、返答中は黙って10〜20ターン続ける。今回の誤検出は16ターン目なので、初回だけで判断しない。
3. 次の返答の途中に「ちょっと待って、こんにちは」など声を重ね、止まった後も続けて話す。停止前の音声はSTTに引き継がないため、話し始めの欠けと停止後の認識を分けて確認する。
4. 再生のみ・介入ありを交互に3〜5回試し、誤停止・取りこぼし・2回目以降の遅延を確認する。ボタンで戻れることも確認する。

`[AEC_TRIGGER]` に発火フレームの `mic/ref/out` と `audio_age_ms`、`[VOICE] trigger_to_record_ms` に発火→録音ON、`trigger_to_first_send_ms` に発火→最初の音声送信成功を出す。`audio_age_ms` は判定に使った最後のマイクフレーム終端から判定までの時間であり、発声開始からの時間ではない。128msの保持・参照の到着待ち・AEC演算があるため、発火後の復帰時間だけを応答全体の遅延としない。Soniox再接続待ちは初回送信の時間に含まれる。

追加の `[AEC_GATE]` は比率で却下した候補窓数 `residual_reject_windows`、飽和フレーム数 `clip_frames`、保護したフレーム数 `recovery_frames` を出す。停止時は `[AEC_TRIGGER] window_retained_pct` と、直前4フレームの `[AEC_GATE_FRAME] index=0..3 mic=... out=...` を確認する。4フレームの詳細は録音の最初の送信後にまとめて出す。停止・録音切替の前にログ出力を増やさないため。

計測へ戻す場合は `AEC_BARGE_DETECT_ONLY=true` で再ビルドする。ボタン割り込みとAEC前後の計測は残る。

## 計測モードでの実機試験（自動停止OFF）

以下は `AEC_BARGE_DETECT_ONLY=true` で、最後まで再生させて比較する手順。

1. v0.7を書き込み、起動ログの `[AEC] ready=1` と `[AEC_MEM]` を確認する。`init failed` や音量計測だけの表示ならAECは動いていない。
2. 再生中は黙って、2〜3ターン会話する。声による停止が起きないこと、再生速度・音切れ・録音復帰に問題がないことを確認する。
3. 次の返答の途中に声を重ねる。今回も声で止まらないのが正常。その後、ボタンで停止して通常STTへ戻れることを確認する。
4. 黙っていた回・声を重ねた回それぞれの `[AEC_LEVEL]` / `[AEC_STATS]` と、発声中の `[AEC]` 行を残す。終了サマリは次のSTT音声の最初の送信成功後に出る。Soniox再接続中は遅れる。
5. 有効な比較が取れたら10ターン以上の会話でメモリ・音切れ・切替時間を確認する。新しいI2S構成の安定性はv0.6の10ターン結果だけでは保証しない。

| ログ | 意味 |
| --- | --- |
| `[AEC] mic / ref / out` | 同じ処理フレームのマイク入力・参照・AEC出力RMS。`mic_max / out_max` は直前約1秒の最大値 |
| `reduction_db` | 参照音がある有効フレームでの入出力エネルギー比。大きいほど出力が小さい。条件がなければ `nan`。音響測定のERLEや音源識別の証明ではない |
| `[AEC_LEVEL] mic_sustained / out_sustained` | 有効・ウォームアップ後の128ms持続値。再生のみと声ありで、処理後の値が分かれるか比較する |
| `paired / missing` | 処理できたフレーム / 参照不足で除外したフレーム。開始境界で少数のmissingはあり得るが、継続的に増える場合は整列を調べる |
| `mic_drop / ref_drop / pending_drop` | 受渡し・保留領域の溢れ。音声処理が追いついているかの手掛かり |
| `clock_resets / format_errors` | サンプル連続性の喪失 / 想定と異なるDMA形式 |
| `clips` | 評価に使ったマイク入力の16bit飽和サンプル数 |
| `cpu_max_us / slow_frames` | 1フレームの整列・AEC・集計にかかった最大時間 / 32msを超えた回数。ISRコピーと参照フィルター等を含む全CPU使用率ではない |

再生のみで出力が下がることに加え、人の声が残るか、欠落で評価区間が減っていないか、通常会話が安定するかを確認する。自動停止の実験と、安定版への採用判断は分ける。

## 初回の実機結果（2026-09-10 00:36〜00:37）

ユーザー提供の `スクリーンショット 2026-09-10 003635.png` / `003710.png` / `003748.png` の順でgeneration 1 / 2 / 3を確認した。3回目はユーザーが「介入あり」と明示。1・2回目は直前の試験手順に沿った再生のみの回として比較する。起動時の `[AEC_MEM]` は今回の画像に含まれないが、`paired` と処理後の値があり、AEC処理の実行は確認できる。

| 回 | 条件 | mic_peak | mic_sustained | out_peak | out_sustained | reduction_db |
| --- | --- | ---: | ---: | ---: | ---: | ---: |
| 1 | 再生のみとして比較 | 4,605 | 2,863 | 820 | 750 | 11.4 |
| 2 | 再生のみとして比較 | 6,768 | 3,760 | 1,578 | 729 | 11.1 |
| 3 | 声の介入あり | 4,502 | 1,311 | 1,279 | 1,123 | 6.7 |

`sustained` は128ms窓内の最小RMSを各窓で計算した、そのターンの最大値。平均音量ではなく、入力と出力の最大窓が同じ時刻とは限らない。`reduction_db` は参照が有効な区間の入出力エネルギー比であり、人の声と再生音を別々に測定した値ではない。

| 回 | paired | cpu_max_us | 再生underruns | amp_to_mic_ms | amp_to_send_ms |
| --- | ---: | ---: | ---: | ---: | ---: |
| 1 | 251 | 23,613 | 0 | 4 | 37 |
| 2 | 228 | 23,709 | 0 | 4 | 38 |
| 3 | 199 | 24,280 | 1 | 4 | 37 |

3回とも `missing=0`、`mic_drop=0`、`ref_drop=0`、`pending_drop=0`、`clock_resets=0`、`format_errors=0`、`clips=0`、`slow_frames=0`。`held_discarded=3` は終了時に保留した3フレームを捨てた値で、実装どおり。AECタスクの `stack_free=5856`、録音前の `ALLOC_FAIL total=0` / `HEAP_CHECK ok=1` も確認した。3回目の再生バッファ不足1回の原因は画像だけでは特定できない。音切れの体感や長時間の安定性を、この3回で確定しない。

1・2回目の結果は再生音の抑制を示す。3回目の持続出力1,123は再生のみの最大750の約1.50倍で、人の声が残る可能性はあるが、返答内容・音量・発声位置が同一ではなく、声の保持を証明する比較にはまだ足りない。瞬間的な最大値は再生のみの1,578が介入ありの1,279を上回るため、瞬間ピークだけで自動停止を決めない。

この初回結果を受け、ファームを変えず、同じ設置位置・音量で「黙って再生を聞く回」と「再生の途中に声を重ねる回」を交互に試す方針とした。その追試結果を以下に記録する。

## 交互試験5回の結果（2026-09-10 00:42〜00:45のキャプチャ）

ユーザーが各回を明示し、1・3・5回目は「ただ再生」、2・4回目は「介入あり」。添付順は5→4→3→2→1だったため、画像の添付番号・保存時刻ではなくユーザーのラベルとgenerationで対応させる。初回3ターンとは別の試験系列として記録する。

| 回 | 画像名の末尾 | 条件 | mic_peak | mic_sustained | out_peak | out_sustained | reduction_db |
| --- | --- | --- | ---: | ---: | ---: | ---: | ---: |
| 1 | 004553.png | 再生のみ | 5,839 | 2,524 | 1,894 | 832 | 11.8 |
| 2 | 004429.png | 介入あり | 5,498 | 2,559 | 2,018 | 1,660 | 10.0 |
| 3 | 004328.png | 再生のみ | 4,927 | 1,876 | 1,834 | 789 | 10.7 |
| 4 | 004312.png | 介入あり | 6,885 | 3,606 | 6,911 | 1,720 | 2.7 |
| 5 | 004242.png | 再生のみ | 16,592 | 7,269 | 16,368 | 7,192 | 1.9 |

1〜4回目では介入ありの持続出力が再生のみの約2倍になる一方、5回目の再生のみは両方を大幅に上回る。この5回をまとめて分離できる固定の音量閾値はない。5回目は未解明の例として残す。

5回目は `clips=66`。これはマイクのDC除去・16bit変換時に飽和した**サンプル数**で、物理マイクの飽和や原因が再生音であることを直接示す値ではない。AEC前の入力も大きいため、AECの出力だけが増幅された事象とは判断しない。最初に見える約1秒の行では `mic_max=16592 out_max=16368 reduction_db=nan`、その行の直近フレームは `mic=741 ref=54 out=844`。最大値と直近フレームは別の時刻の可能性があり、`ref=54` をピーク時の参照音量として扱わない。`nan` は有効な参照区間の入出力比が計算されていないことを示す。このログだけでは物音・接触・マイク入力の過渡変化・再生参照の対応・AEC状態の影響を区別できない。

| 回 | paired | missing | clips | cpu_max_us | 再生underruns | amp_to_mic_ms | amp_to_send_ms |
| --- | ---: | ---: | ---: | ---: | ---: | ---: | ---: | ---: |
| 1 | 192 | 0 | 0 | 25,819 | 0 | 4 | 38 |
| 2 | 200 | 0 | 0 | 24,340 | 1 | 4 | 38 |
| 3 | 202 | 0 | 0 | 24,472 | 1 | 4 | 37 |
| 4 | 129 | 1 | 0 | 27,319 | 1 | 3 | 36 |
| 5 | 170 | 0 | 66 | 25,820 | 1 | 4 | 37 |

5回とも `mic_drop=0 ref_drop=0 pending_drop=0 clock_resets=0 format_errors=0 slow_frames=0`、`held_discarded=3`、録音前の `ALLOC_FAIL total=0` / `HEAP_CHECK ok=1`。4回目の参照不足1フレームと、2〜5回目の再生バッファ不足各1回は残る。処理の計測値だけでは以前の継続的な受信停止・クラッシュは再現していないが、音響面の安定を意味しない。

ユーザーから「触ってその衝撃で大きくなったかも」と補足があり、まず介入を試す依頼を受けた。接触が原因と確定したわけではない。AECの音響設定を維持し、上記の仮閾値で自動停止を有効化した。最初は置いたまま触らず再生のみを試す。再発した場合は `[AEC_TRIGGER]` の同じフレームの入力・参照・出力と `clips` を確認する。

## 自動停止の試験とTLS接続失敗（2026-09-10 01:20）

ユーザーの報告は「少なくとも再生音では止まらない」「少し反応が悪い」、その後に再生しなくなったというもの。`スクリーンショット 2026-09-10 012053.png` ではgeneration 13で以下を確認した。

- Lambda接続前は内部RAM `free=61240 max_blk=17396`。`lambda_connect_ms=34 ok=0`、`connect() FAILED`。
- 次の録音前の `ALLOC_FAIL delta=1 total=19 last_size=16717 last_caps=0x00000804`。capsは内部RAMと8bitアクセスの指定。累積19は会話回数ではない。
- `HEAP_CHECK ok=1`。その時点のヒープ整合性検査は通るが、断片化やリークの不存在を保証しない。
- `AEC_LEVEL gate_fired=0`、`AEC_STATS paired=0`。この回はAECで止めたのではなく、Lambdaの接続失敗で音声受信へ進めなかった。`reduction_db=nan` は評価データなし。
- 失敗後はマイクを再初期化し、Sonioxへ再接続して録音に戻っている。クラッシュのログではない。

接続中の内部RAM確保失敗は確認でき、TLS作業領域が有力な対象。接続前の最大ブロックが16,717 bytesより大きくても、途中の複数の割り当てや他タスクとの同時使用で不足し得る。AEC追加分・会話履歴・一時バッファ・断片化・リークの寄与はこの1枚で確定しない。旧相槌Stringリーク対策はv0.7にも残っている。以前の[調査](esp32-s3-tls-memory-investigation-2026-09-06.md)で保留していたTLSのPSRAM移行を、今回v0.7に適用した。

まず修正版で20ターン程度、再生のみと介入を混ぜて再発を確認する。起動時の `[TLS_MEM] ... ready=1` と、接続時・会話境界の `fail=0`、`ALLOC_FAIL delta=0`、PSRAM空きを見る。介入の閾値1,200・保持128ms・参照待ち96msは維持した。「反応が悪い」が取りこぼしなのか、止まるまでの時間なのかを確認し、前者はAEC出力の持続値、後者は `[AEC_TRIGGER] audio_age_ms` と録音・初回送信までの時間で調整する。

## TLS修正後の反応・録音・本返答の遅れ（2026-09-10 01:36）

ユーザーがTLS修正版を書き込んだ後と確認した `スクリーンショット 2026-09-10 013647.png` のgeneration 9を記録する。再生音では止まらず、声で止まるようだが動作が鈍く、録音認識と相槌後の本返答も悪いとの報告。

- `AEC_TRIGGER mic=2010 ref=0 out=2387 threshold=1200 hold_ms=128 audio_age_ms=117`、`gate_fired=1`。この停止はAEC閾値判定によるもの。発火音源が人の声かどうかをこの行だけで確定しない。
- 発火→録音31ms、発火→初回送信64ms。終了処理ログのアンプOFF→マイク4ms、送信38ms。全体の遅れをドライバ解放・再確保だけに帰さない。音声フレームは判定時点で117ms古く、発火前の待ちがある。
- `TLS_MEM psram=1 calls=8179 fail=0 largest_req=20000`、`ALLOC_FAIL delta=0 total=0`、`HEAP_CHECK ok=1 internal_free=181144 max_blk=86004`。この系列では確保失敗が出ていない。全体の遅さが解消した証拠ではない。
- AEC `paired=137`、欠落・時計リセット・飽和・32ms超過はいずれも0、`cpu_max_us=26398`。最大値は平均CPU使用率ではない。
- 録音再開後の最初のSTT集計は `peak=32767 raw0=0x00000000`、後続は3,585 / 4,383。開始時のゼロ埋め・DC補正の過渡応答を調べる対象。実際の入力過大や認識不良の原因をこの値だけで断定しない。

この結果に対する変更:

1. AECの固定96ms待ちを、必要な参照到着後すぐ処理する方式へ変更。未到着時の上限96msと全参照検証を維持。最初の非ゼロTX波形前はAEC演算を省く。
2. `SttMicFilter.h` で録音開始ごとにDC推定を初期化し、最初の非ゼロサンプル群の平均から開始する。起動時の完全なrawゼロは無音として出し、DC推定へ混ぜない。小数精度を保持して整数丸めの偏りを抑える。AEC側の入力変換・閾値は変更していない。
3. 停止理由、Soniox処理のブロック時間、本文テキスト・TTSヘッダーを処理した時刻、最初の送信ブロックの変換統計を追加。

| 追加ログ | 読み方 |
| --- | --- |
| `[TURN_STOP] cause=... ws_max_block_ms=...` | 通常の応答終了経路で `aec_level` / `button` / `stream_error` / `completed` を区別。AEC閾値による停止は音源を証明しない。Lambda接続失敗など受信前の失敗は既存の失敗ログを見る |
| `[WS_TIMING] stage=... blocked_ms=...` | `ws.loop()` が50ms以上戻らなかった呼び出し。受信中・末尾再生中・録音中等の段階を表示。TLS・通信待ち・CPU競合・イベント処理の合計で、TLSだけの所要時間ではない |
| `[LATENCY] segment_text_ms=...` / `segment=... tts_header_ms=...` | 返答ターン開始からメタデータを処理した時刻。接続・ヘッダー・最初のPCM・I2Sコピーの既存ログと比較する。サーバーの生成時刻や実際の発音開始ではない |
| `[STT_INPUT] first_block_samples=... dc=... clips=... zero_samples=...` | 最初に送信成功したPCMブロックのDC推定、変換時の飽和数、完全なrawゼロの数。5秒単位のSTTピーク統計と別に確認する |

閾値1,200・保持128ms・I2S構成・相槌と文間400ms・TLSのPSRAM割当は維持。**停止前の音声をSTTへ引き継ぐ機能は未実装で、話し始めが欠ける制約は残る。** Soniox未接続時の録音保持も未対応。本返答の遅延は今回の画像には開始区間がなく、まだ原因を特定していない。

再試験では同じv0.7を書き込み、端末を触らず再生のみ→介入ありを交互に試す。`audio_age_ms` と録音開始時の飽和、欠落・誤停止を比較する。聞き取りは「停止前の語」と「停止後に続けた語」を分ける。本返答が遅い回は相槌から最初の本文までの `[LATENCY]` / `[WS_TIMING]` を残す。

### 参照待ち修正後の体感報告と次の切り分け

ユーザーは「ちゃんと反応して止まる」「再生音自体も問題なし」と報告。一方で、v0.6では問題なかった会話全体の遅れを感じるとのこと。この追試の数値ログは未受領のため、反応時間の改善幅・誤停止率・録音認識の改善は確定しない。

コード上ではAEC監視がCore 1 / 優先度2、Arduinoの本文受信・STT・Soniox処理が標準設定でCore 1 / 優先度1。v0.6の軽い音量集計を重いAECへ置き換えたことで、同じコアの通信処理が待たされる可能性がある。以前の `cpu_max_us=26398` は32msフレームに対する最大処理時間であり、平均使用率が約82%と測定されたわけではない。

手元のWebSocketsライブラリでは `WebSocketsClient::loop()` 内でTLSの `connect()` を同期実行する。スケッチは本文のバイナリヘッダー受信後とPCM受信中にもこれを呼ぶため、再接続が長引くと本文受信も止まる。v0.6にもこの呼び出しはあるので、構造の存在だけでv0.7の遅延原因と断定しない。

まず遅い1ターンの `Sending to Lambda` から `first_tts_i2s_ms` までを確認し、`BC wait done` / `Backchannel phase done` / `[LATENCY]` / `[WS_TIMING]` のどこが延びたかを調べる。録音中はAEC監視を停止しているため、話し終わりから相槌までの遅れには録音・endpoint・相槌取得など別の候補もある。追加したログで区間が分かるまでは、処理コア・優先度・閾値の変更を重ねない。

## 相槌後の本返答待ちと先行接続の分離（2026-09-10 12:49）

ユーザーは、遅いのは「相槌が出てから本返答が始まるまで」で、一度再生が始まれば途切れないと補足。マイク感度が若干悪く感じるが普通に文字起こしはできており、まだ印象の段階とのこと。声への停止反応・再生音は良好。`スクリーンショット 2026-09-10 124900.png` の1ターン目から以下を確認した。

- `[TURN_STOP] cause=completed ws_max_block_ms=1842`。再生中の `ws.loop()` が一度1,842ms戻らなかった。サマリだけではその呼び出しの段階は分からず、全時間が相槌と本返答の間に加算されたとは断定しない。
- 画像上部にSoniox接続完了があり、3番目のTTSヘッダー処理はターン開始後3,777ms。最初の本文開始ログは画像範囲外。
- `underruns=0`、AEC `paired=276 missing=0 mic_drop=0 ref_drop=0 pending_drop=0 clock_resets=0 format_errors=0 clips=0 slow_frames=0 cpu_max_us=24000 held_discarded=1`。受信・AECが継続している。
- `ALLOC_FAIL delta=0 total=0`、`TLS_MEM psram=1 fail=0`、録音前の内部RAM空き185,164 bytes。今回も確保失敗の停止ではない。
- マイク再準備5ms、アンプOFF→送信39ms。STT最初のブロックは `dc=-11059 clips=1 zero_samples=7`。開始時の過大値は完全には解消していない。AECの `clips=0` とSTTの `clips=1` は別の区間・変換処理であり混同しない。マイク感度低下を証明する比較データはない。

### 今回の変更

`SonioxPreconnect.h` に起動時に一度作成するCore 0 / 優先度1 / スタック8KBの先行接続タスクを追加。相槌前に開始し、TLS接続・WebSocket upgrade・Soniox開始メッセージ送信までを本文受信と並行して実行する。本文受信とAECのCore 1、再生タスクのCore 0 / 優先度2は維持する。AECの設定、再生音量、STTの変換・ゲインは今回変更しない。

先行接続中はワーカーだけがWebSocketへアクセスする。状態の公開・受取はrelease/acquireで同期し、ワーカーが完全に使い終わった後にloopへ戻す。ワーカーのコールバックは接続時の開始メッセージ送信だけを行い、録音フラグ・認識テキスト・相槌・LEDを変更しない。通常コールバックへの復帰と接続完了のアプリ処理はloopで行うため、開始メッセージを二重送信しない。

待機中の `serviceSoniox()` は直ちに戻り、本返答の受信を進める。接続完了後のWebSocket処理は従来どおりloopが担当し、再生中に再接続が必要になった場合は再びワーカーへ渡す。起動時のワーカー作成に失敗した場合はログを出し、従来の同期処理へ戻る。

録音再開時に接続がまだ終わっていない場合は待ちが残る。再試行期間の5秒を過ぎても、個別の同期TLS呼び出し自体が戻っていないことがある。その場合もソケットを別タスクから破棄・再初期化せず、所有権を保持して完了を待つ。BLEへ移る際のキャンセルも同じで、使用中のタスクを強制削除しない。Sonioxが未接続の間の音声保持と、検出前の音声引継ぎは今回も未実装。

### 実機で確認するログ

- 起動時 `[WS_PRECONNECT] worker_ready=1 stack_bytes=8192 core=0`、各ターンの `started background=1` を確認。
- 完了時 `[WS_PRECONNECT] elapsed_ms=... ready=1 cancelled=0 stack_free=...`。これは並行した接続準備の所要時間で、本文受信を止めた時間ではない。`[TURN_STOP] ws_max_block_ms` と分けて評価する。
- 相槌後の待ち、`first_pcm_chunk_ms` / `first_tts_i2s_ms`、本文受信側の `[WS_TIMING]` を前版と比較。返答内容・ネットワーク・サーバー側所要時間も変わるため、1回で改善量を確定しない。
- 再生のみ→声で停止を交互に試し、再生の連続性・停止後の録音・AEC欠落・確保失敗・新ワーカーのスタック余裕を確認する。接続準備完了前の早い停止は通常より録音開始が遅れる可能性がある。

## 先行接続分離後の実機結果と残課題（2026-09-10 13:19）

ユーザーから「めちゃくちゃよくなった」「本文再生もスピーディーになった」と報告。一方、会話を続けると本文が再生されなくなるとの指摘があり、`スクリーンショット 2026-09-10 131906.png` の16ターン目を確認した。この到達点を保存し、停止の調査は次の作業とする。

- `first_pcm_chunk_ms=3241`、`first_tts_i2s_ms=3276`。このターンは本文の受信・再生が始まった後に中断している。
- `[TURN_STOP] cause=aec_level ws_max_block_ms=2`。分離前の12:49の1,842msとは別のターンなので、本文開始が正確に1,840ms短縮したという比較ではない。
- `[AEC_TRIGGER] generation=16 mic=5822 ref=990 out=1304 threshold=1200 hold_ms=128 audio_age_ms=82 detect_only=0` の直後、PCM読み込みが介入によりキャンセルされている。AEC判定が直接の停止理由。検出した音がユーザーの声・再生音・接触音のどれかは、この画像だけでは確定できない。
- `trigger_to_record_ms=29 ws_ready=1`、`trigger_to_first_send_ms=62`。停止後は録音へ戻り送信を再開している。
- `ALLOC_FAIL delta=0 total=0`、`TLS_MEM psram=1 fail=0`、録音前の `HEAP_CHECK ok=1 internal_free=164000 max_blk=65524`。この画像では確保失敗による停止は出ていない。
- AECは `paired=86 missing=0 mic_drop=0 ref_drop=0 pending_drop=0 clock_resets=0 format_errors=0 slow_frames=0`。`clips=318` はターン集計値であり、発火したフレームのクリップや音の由来を示すものではない。入力過渡も含め次回切り分ける。

本文開始の体感改善は確認できたが、継続会話中の停止と、接続失敗・キャンセル時の復帰や長時間の安定性は引き続き確認が必要。

## 無発声での誤検出への対策（2026-09-10、13:19ログへの補足）

保存コミット `dd77e42` の後、ユーザーが「俺何も話してない」と補足。この停止は意図した声による介入ではなく誤検出として扱う。再生音の残り・接触音・マイク入力の乱れのどれかは、引き続き音声データなしでは特定できない。

発火フレームは `mic=5822 out=1304`（約22.4%）で、強く抑制された出力でも絶対閾値1,200を超えると止まる実装だった。また、ターンの `clips=318` に対し、従来は飽和した当該フレームを除外するだけで、その後の保護期間がなかった。この二点に対して以下を追加した。

- 同じ128ms候補窓で、出力RMSが入力の25%以上残る条件。固定閾値を一律に上げず、強く抑制された入力の残りを却下する試み。25%は公式推奨値ではなく今回の試験値。AEC前後の同時刻窓を比較しても、AEC内部遅延や声と再生音の混合を分離測定できるわけではない。
- 飽和後256ms分の新鮮な非飽和音声で保護。128msの連続判定はその後に始める。声でも飽和すれば反応が遅れるため、近距離・大声の試験も必要。これはAECの回復時間を測定した値ではない。
- 発火した4フレームと、却下・保護の件数を記録。ターン全体の最大値やクリップ数から、発火の直前も同じ状態だったと推定しない。

既存のRMS 1,200 / 128ms、AEC演算・マイク変換・再生・STT・Sonioxの処理は維持する。固定長の小さな窓だけを追加し、動的確保や新しい待機処理は追加しない。NLPを強くする変更は今回は行わない。[EspressifのNLP説明](https://docs.espressif.com/projects/esp-sr/en/latest/esp32s3/acoustic_echo_cancellation/README.html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) も、強い抑制で近端音声に影響する可能性を示している。

試験では①返答中は黙って10〜20ターン、②通常距離の声で介入を交互に確認する。誤停止があれば `[AEC_TRIGGER]`、`[AEC_GATE_FRAME]`、`[AEC_GATE]` を確認し、反応しなくなった場合は `[AEC_LEVEL]` と `[AEC_GATE]` を見る。画像に実際の候補4フレームはないため、今回の変更で当時の停止を必ず防げるとはまだ言えない。

## 状態持越しの切り分け（2026-09-10 18:26）

誤検出保護版についてユーザーから「めちゃくちゃいい感じ」だが、最後に自分の再生音で割り込んだかもしれない、AECが徐々にずれることはないか、との報告。`スクリーンショット 2026-09-10 182613.png` のgeneration 7は以下の状態だった。発火時に無発声かつ非接触だったかは未確認で、音源の断定はしない。

- `[AEC_TRIGGER] mic=1415 ref=917 out=4527 audio_age_ms=84 window_retained_pct=91.6`、`cause=aec_level`。今回もAECのゲートが直接の停止理由。
- 発火直前4フレームは、古い順に `mic/out=3167/1348, 6786/2819, 4827/6164, 1415/4527`。後半は出力が入力より大きいが、AEC内部の時間遅れも含む値なので、これだけで増幅・発散・同期ずれと断定しない。
- `residual_reject_windows=0 clip_frames=0 recovery_frames=0`。今回の窓は91.6%残っており、25%の比率条件で却下する対象ではない。入力飽和もなく、前回の保護だけではこの候補を防げない。
- `paired=106 missing=0 mic_drop=0 ref_drop=0 pending_drop=0 clock_resets=0 format_errors=0 clips=0 slow_frames=0 cpu_max_us=23376`。大きな欠落や時計の不連続は記録されていない。`clock_resets=0` は小さな時間ずれや、実際の音響経路と参照のずれを否定するものではない。
- `underruns=0 ws_max_block_ms=26`、`trigger_to_record_ms=30 trigger_to_first_send_ms=63`。`ALLOC_FAIL total=0` / `TLS_MEM fail=0`。通信・再生の詰まりによる停止を示すログではない。

コード上、時計・参照履歴・マイクDCは毎ターン初期化している一方、AEC本体の学習済みフィルターと内部の音声履歴は持ち越していた。録音中はAECに音声を渡さず、マイク/再生I2Sもターン間で作り直すため、次ターンを連続した同じ音声列として扱う状態持越しが影響する可能性がある。これは調査仮説であり、今回の原因と確定したものではない。

比較のため `AecMonitor.h` に `AEC_RESET_EACH_TURN=true` を追加。インストール済み `esp_aec.h` に公開のreset APIがないため、`aec_destroy()` → `aec_create_from_config()` で本体だけを作り直す。前の監視タスクの停止確認後、今回のcapture・監視タスクの開始前にloopが実行する。ISRは本体へ触れない。古い本体を解放してから同じ設定で確保し、2個分のAEC領域を同時には保持しない。失敗したターンは自動停止しない生マイク計測へ戻り、確保済み作業領域を保持して次のターンで再試行する。

閾値・比率・飽和後の保護・500msのウォームアップ・参照の16ms advance・NLP強度は変更しない。`[AEC_RESET] generation=... enabled=1 recreated=1 ready=1 elapsed_us=...` が2回目以降の成功ログ。1回目は `recreated=0`。作り直す所要時間は相槌再生前の準備に加わるので、`elapsed_us` と体感速度を確認する。再学習が必要になることで、ターン冒頭の抑制が弱くなる可能性もある。

同じ配置・音量で、返答中は無発声・非接触の会話を10〜20ターン、その後に声での介入を確認する。`[AEC_RESET]` と、正常終了/誤停止双方の `[AEC_LEVEL]` / `[AEC_STATS]` / `[AEC_GATE_FRAME]` を残す。`AEC_RESET_EACH_TURN=false` で再ビルドすると、直前の誤検出保護版と同じ本体持越しに戻せる。改善しなければ、マイク/参照/出力の波形を保存して遅れ・相関を測り、固定の参照ずれや再生音の変化を調べる。

## 再初期化版の実機結果と本文開始の待ち（2026-09-10 18:43）

ユーザーから「だいぶ良くなった」「ちゃんと自分の声でキャンセルされるし、再生音ではキャンセルにならない」と報告。この状態をコミットするよう依頼があった。一方、全体、特に本文開始が重く感じるとの指摘もあり、速度の改善を完了扱いにはしない。

`スクリーンショット 2026-09-10 184341.png` の10ターン目では、以下を確認した。今回の停止はユーザーの声での介入という報告に沿って扱い、誤検出と決めつけない。

- `[AEC_TRIGGER] mic=565 ref=9748 out=1816 audio_age_ms=74 window_retained_pct=107.8`、`[TURN_STOP] cause=aec_level ws_max_block_ms=45`。検出後は録音へ29ms、初回送信へ62msで復帰している。
- `underruns=0`、`ALLOC_FAIL delta=0 total=0`、`TLS_MEM psram=1 fail=0`。今回の画像に、再生の供給不足や確保失敗は出ていない。
- AECは `paired=412 missing=0 mic_drop=0 ref_drop=0 pending_drop=0 clock_resets=0 format_errors=0 clips=0 slow_frames=0 cpu_max_us=30977`。最大処理時間は32msのフレーム間隔に近いが、これは1フレーム処理の最大経過時間で、平均CPU使用率でも、毎フレーム約31msを消費するという測定でもない。
- `[AEC_RESET]` と、この返答の要求開始〜最初の本文再生のログは画像範囲外。改善報告は得られたが、本体再初期化が原因に効いたこと、再作成の成否・所要時間、長時間の再確保の安定性は、この画像だけで確定しない。

コード上、速度への影響を調べる候補は残っている。

- `startVoiceMonitor()` のAEC本体再作成はloopで同期実行し、相槌再生より前に行う。その時点でLambda接続・要求送信のタスクは既に起動しているため、初期化時間が本文開始にそのまま加算されるとは限らない。相槌の後に新しい固定待ちを挿入する処理でもない。まず `[AEC_RESET] elapsed_us` で実際の所要時間を確認する。
- AEC監視はCore 1 / 優先度2、本文を受信・解析するloopはCore 1 / 優先度1で動くため、演算と受信処理の競合は候補になる。ただし、上記の最大値だけでは今回の待ちの原因と判断できない。
- Lambda接続、LLM・TTS生成、受信待ち、相槌終了時点も分けて確認する。同じ遅いターンの `Sending to Lambda` から `first_tts_i2s_ms` までを残し、`AEC_RESET`、`BC wait done`、`Backchannel phase done`、`lambda_connect_ms`、`lambda_send_ms`、`headers_ms`、最初の `segment_text_ms / tts_header_ms / first_pcm_chunk_ms` を比較する。

保持128ms、ウォームアップ500ms、飽和後256msは割り込み検出の条件であり、本文再生をその時間sleepさせる処理ではない。セグメント間400msは従来から維持している。今回の保存時点では、遅延への追加修正やファーム書き込みは行っていない。

## 相槌の再生予定を本文要求へ反映（2026-09-10）

ユーザーの指定で高速化検討の候補②だけを実装。相槌取得の並行化は保留、本文のプリバッファ32KBは維持する。別途ユーザーが更新したESP32/App用Lambdaの検索後の前置き抑制プロンプトには手を加えない。ローカルESP32用Lambdaには既存の `body.backchannel_fired` による本文冒頭の相槌省略指示が残っていることを確認した。

従来は、相槌を再生する前にPOSTを組み立てるため、再生後にtrueとなる `backchannelFired` をそのまま送るとfalseになっていた。要求直前に「キャンセルされておらず、相槌ready、PCMあり、サイズが正」を `backchannelPlanned` として固定し、`backchannelFired || backchannelPlanned` を既存APIの `backchannel_fired` に送る。実際の相槌再生も同じ予定を使うので、要求後の遅着で相槌だけが追加されることを避ける。

取得なし・音声なし・サイズ0なら予定はfalse。実再生用の `backchannelFired` は従来どおり再生処理後に更新し、STT・相槌の再取得抑制・統計のために先回りしてtrueにはしない。本文要求は再生終了を待たず、現在の接続・再生の順序を維持する。

このAPI値は「本文前に端末が相槌を担当する」という通知で、音響上の再生完了を保証するものではない。通知後のI2S/割り当て失敗やキャンセルまでPOSTに遡って反映することはできない。LLMへの指示なので前置きが必ずなくなる保証もなく、検索前の一言やキャラクター固有の言い回しとは分けて評価する。

実機では通常どおり相槌を伴う会話を複数回行い、以下を確認する。

- 要求前の `[BC] reply_hint=1 planned=1 played=0 pcm_bytes=...`。以前はこの場面で `backchannel_fired=false` を送っていた。
- 続いて相槌を再生し、本文が同じ相槌・挨拶を繰り返さず、本題から始まる傾向になること。
- 相槌がないターンでは `reply_hint=0 planned=0 played=0 pcm_bytes=0`。無条件で省略を指示していないこと。
- AECの声での停止、再生音による誤停止、音切れが従来どおりであること。短い前置きを省くと最初の文が長くなる場合があるため、最初の発音が早くなることと、本題に早く入ることを分ける。

検証：Arduinoコア3.3.11 / IDF 5.5.5、PSRAM enabled / Flash 4MB / no_fs / USB CDC enabledでコンパイル・リンク成功。Flash 1,470,778 / 2,031,616 bytes（72%）、静的RAM 67,096 bytes（20%、保存点と同じ）。本文POSTと相槌再生が同じ予定を参照すること、PCMなしの場合に通知しないこと、実再生フラグを早めに変更しないことをコードで確認した。20:09にユーザーから「いい感じになったかも」と報告。画像は検索付きの会話で通知ログは範囲外のため、通常会話での前置き抑制と通知値の対応は未確認。

## 持ち上げて使った会話での停止（2026-09-10 20:09）

ユーザーは会話中に再生が止まると報告し、今回は端末を持ち上げたりしていたが、ぶつけて音を出したわけではないと補足。`スクリーンショット 2026-09-10 200958.png` の11ターン目では以下を確認した。

- `[AEC_TRIGGER] generation=11 mic=1732 ref=925 out=1666 threshold=1200 hold_ms=128 audio_age_ms=79 window_retained_pct=92.5` の後、`[TURN_STOP] cause=aec_level ws_max_block_ms=26`。直接の停止理由はAECの音量ゲート。
- 現行ゲートでは、4フレームの出力RMSが各1,200以上であり、同じ窓の出力/入力RMS比が25%以上なら候補になる。今回92.5%なので比率条件は通る。92.5%を「再生音が92.5%残った」「人の声である」と解釈しない。入力と出力には内部遅延もあり、音源の識別値ではない。
- 検出→録音31ms、初回送信64msで復帰。`ALLOC_FAIL delta=0 total=0`、`TLS_MEM fail=0`。`underruns=2` もあるが、これは別の再生供給不足の記録で、この停止の理由を示す値ではない。
- 直前の定期ログでは `missing=0 mic_drop=0 ref_drop=0 cpu_max_us=26361`。ターン最後の `[AEC_LEVEL] / [AEC_STATS] / [AEC_GATE] / [AEC_GATE_FRAME]` は画像範囲外。飽和・時計リセット・直前4フレームの全状態を確定しない。

仮説：持ち上げ・持ち替えで、机からの反射や手による遮りなどが変わり、再生音のマイクへの入り方が変化した可能性がある。衝突音がなくても音響経路は変わり得る。AECが環境変化に再適応することは [XMOSのAEC説明](https://www.xmos.com/documentation/XM-014600-PC/html/doc/user_guide/audio/1_Automatic%20Echo%20Cancellation%20%28AEC%29.html) にも記載があるが、これは本機のEspressif AECの追従時間や今回の原因を測定したものではない。

現行コードはAEC後の音量判定であり、人の声と消し残った再生音を分類する処理ではない。毎ターン初期化はターン間の状態持越しへの比較策で、再生途中の音響変化を直ちに解決するものではない。この報告時点では停止直前の発声・移動タイミングが不明だったため、以下の追加試験へ進んだ。

## スピーカーの向きを変えた追加試験（2026-09-10、20:09の報告後）

ユーザーが条件を変えて比較し、次の結果を報告した。各条件の回数・継続時間や、そのときの追加ログは未提供なので、この比較の範囲での結果として扱う。

| 条件 | ユーザーの観察 |
| --- | --- |
| 机に置いたまま | 問題なし |
| 最初から手に持って静止 | 問題なし |
| 再生途中に持ち上げる | 問題なし |
| スピーカーをマイクへ向ける | 再生が停止した |

スピーカーは長い線でつながっており、端末へ固定されていない。持ち上げ時にスピーカーの向きが変わり、マイクへ向くことがあり得るという説明だった。今回の結果では、持ち上げそのものよりスピーカーとマイクの相対的な配置・向きが手掛かりになる。20:09の停止が全く同じ条件だったことまで確認できたわけではない。

想定する原因は、向きを変えたことによる音響経路やマイク入力レベルの変化。AECの再適応中に一時的に再生音が残る場合、固定後も抑制しきれない場合、入力が飽和する場合をまだ区別できていない。この報告だけで、会話を重ねるほどAECのサンプル時計がずれると判断しない。

次の確認は以下の順序とする。

1. スピーカーとマイクを実際に使う位置・向きへ固定し、同じ再生音量で、無発声の連続再生と声による介入を比較する。
2. マイクへ向けた条件も調べる場合は、最初からその向きで固定した場合と、再生途中に向きを変えた場合を分ける。変えた直後だけの停止か、固定しても繰り返し止まるかを記録する。
3. 停止時の `[AEC_TRIGGER] / [AEC_LEVEL] / [AEC_STATS] / [AEC_GATE] / [AEC_GATE_FRAME]` を確認する。原因をさらに絞る必要があれば、マイク・参照・出力波形を記録し、実際の遅れや飽和を比較する。

調整余地は残っている。AEC本体では参照の整列やNLP強度、後段ではRMS閾値・保持時間・比率条件が候補。この時点のNLPは `AEC_NLP_LEVEL_NORMAL`（2026-09-12にAGGRへ変更、下記「後続の変更」）で、[Espressif公式説明](https://docs.espressif.com/projects/esp-sr/en/latest/esp32s3/acoustic_echo_cancellation/README.html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) では、より強い設定は残留エコーを抑える一方で近端の声にも影響するとされる。改善量は実機比較が必要で、今回の追加試験後は設定・コードを変更していない。閾値を上げたり保持を延ばしたりする場合も、誤停止だけでなく声の取りこぼし・反応時間を比較する。

## 後続の変更（2026-09-12）

AC RMS判定への移行は [AC RMS判定と到達点](esp32-aec-gate-ac-2026-09-12.md)、入力1/4縮小の却下は [入力クリップ比較](esp32-aec-input-headroom-2026-09-12.md)、終端救済は [終端調査](esp32-stream-end-investigation-2026-09-12.md)、USBログ待ちは [USBログ待ち対策](esp32-usb-log-backpressure-2026-09-12.md) に記録。ここには個別メモを統合した2件を残す。

### NLPをAGGRへ変更

- 無発声時の誤停止（turn=18、out_sustained=1,410）と意図した「ちょっと待って」（turn=20、1,463）の差が小さく、固定閾値の引き上げでは分離しにくいため、残留エコー抑制を `AEC_NLP_LEVEL_NORMAL` → `AEC_NLP_LEVEL_AGGR` にした。参照時刻、FD_LOW_COST、filter_length=4、RMS閾値、毎ターン再作成は維持。
- インストール済みコア3.3.11の `esp_aec.h` / `esp_aec_nlp.h` でNORMAL=0、AGGR=1と `config.nlp_level` を確認。現行が呼ぶ `aec_process()` は、Espressif公式説明では線形処理＋非線形処理の一括呼び出し。**NLP呼び出しが欠けていると判断して二重に適用しない。**
- AGGRは近端音声にも影響し得るため、誤停止の減少だけで採用せず、普通の声での停止と反応速度も見る。厳密なA/Bには固定PCM再生経路が要るが現ファームにないため、比較は予備的なもの。ビルド指定は `-DTOYTALKER_AEC_NLP_LEVEL=1`（誤った値やVERYAGGRはコンパイル失敗）。20:03にAGGR版を書き込み、その後の版もAGGRで継続。

### ボタン短押しの即時消音

- 旧実装のGPIO35割り込みは停止フラグを立てるだけで、GPIO39のアンプ消音は本文処理の後始末（接続ワーカー完了待ち、TLS読み込み、相槌のI2S書き込み）を待っていた。音声検出側は監視タスクで直接消音しているため、ボタンの遅れが音声検出にも起こるとは限らない。
- 修正: `BargeInFlag::setFromISR()` でGPIO39をレジスタ操作でLOWにし停止フラグを立てる。ISR内ではSerial・動的確保・I2S/TLS終了を行わない。アンプ有効化も同じクリティカルセクションで停止フラグを確認し、停止後にHIGHへ戻す競合を防ぐ。アンプ出力ピンの初期化後にボタン割り込みを登録。後始末と録音再開は既存経路のまま。
- 20:44の実機結果（ユーザー報告「一瞬で止まる」）:

| turn | ISR→消音GPIO操作（µs） | ISR→録音再開（ms） | ISR→初回STT送信（ms） |
|---|---:|---:|---:|
| 3 | 1 | 39 | 73 |
| 6 | 2 | 58 | 91 |
| 7 | 1 | 57 | 90 |
| 8 | 1 | 65 | 99 |

- 未計測: 物理押下からISRまでの遅延、スピーカーの音響的な停止時間。接続待ち中など全局面の検証は未完了。

## ビルドと復旧

Arduino IDEでは `devices/mcu/esp32_s3/toytalker_mini_v0.7/toytalker_mini_v0.7.ino` を開く。ESP32S3 Dev Module / Flash 4MB / QIO 80MHz / QSPI PSRAM / No FS 4MB (2MB APP x2) / USB CDC Enabledなど、実機で使っている設定を維持する。

```powershell
arduino-cli compile --fqbn esp32:esp32:esp32s3:PSRAM=enabled,FlashSize=4M,PartitionScheme=no_fs,CDCOnBoot=cdc --build-path "$env:TEMP/toytalker_v07_build" devices/mcu/esp32_s3/toytalker_mini_v0.7
```

v0.6へ戻す場合は、そのフォルダーの `toytalker_mini_v0.6.ino` を開いて同じボード設定でUSB書き込みする。現在の保存状態は計測モードなので、音量方式の自動停止を試すときは [v0.6の調整手順](esp32-v06-voice-barge-in.md#調整する定数) に従う。通常会話の安定版へ戻す場合はv0.5を使う。スケッチの切替にFlash全消去は不要。

比較用に `AecMonitor.h` の `AEC_ENABLED=false` とすれば、標準I2S APIのまま音量計測だけで再ビルドできる。音響処理を外す切り分けであり、旧ドライバと同じ条件ではない。旧ドライバへ戻すときはv0.6スケッチを使う。

TLSの確保先だけを比較する場合は `TlsMemory.h` の `TLS_PSRAM_ENABLED=false` で再ビルド・再起動する。コア標準の内部RAM確保へ戻り、今回の接続失敗が再発する可能性がある。実行中の切替は行わない。

初期土台（2026-09-09）の検証: 上記設定・Arduinoコア3.3.10でコンパイル・リンク成功。Flash 1,400,218 / 2,031,616 bytes（68%）、静的RAM 53,624 bytes。作成時は4つのヘッダーがv0.6とハッシュ一致、スケッチの差は説明コメントと起動表示だけだった。

AEC計測版（2026-09-10）の検証: 同じ設定・コアでコンパイル・リンク成功。Flash 1,473,226 / 2,031,616 bytes（72%）、静的RAM 66,640 bytes（20%）。生成ELFで追加した3つのDMA callbackがIRAM、`aecMonitor` が内部DRAMに配置されていることを確認した。旧 `i2s_driver_install` はリンクされていない。AEC・TLS・タスクの動的メモリ使用量は、この静的RAM表示だけでは判断できないため実機ログで確認する。

AEC計測版では `tests/aec_signal_test.cpp` の7件のstatic_assertで、DMA境界をまたぐ24→16kHz参照、欠落・上書き・ターン初期化、小さな時計補正、ローパスのDCゲイン・10kHz除去、サンプル時計の不連続・連番周回、欠落をまたがない持続判定を確認した。既存のHTTP chunked受信・音量判定・集計のコンパイル時テストも通過。これはAECライブラリの音響品質やISR並列動作の実機検証ではない。

AEC自動停止の実験版（2026-09-10）の検証: 同じ設定・コアでコンパイル・リンク成功。Flash 1,464,974 / 2,031,616 bytes（72%）、静的RAM 66,920 bytes（20%）。`tests/aec_signal_test.cpp` に、単発ピークでは止めず4フレーム連続で発火すること・1ターン1回と次ターン再発火、未ウォームアップ・飽和・古い音声・欠落で保持を切ることの2件のstatic_assertを追加した。全9件と既存のHTTP chunked受信・音量判定テストを、インストール済みXtensaコンパイラーの `-std=c++17 -Wall -Wextra -Werror -fsyntax-only` で確認した。

TLS PSRAM修正版（2026-09-10）の検証: Arduinoコア3.3.11 / IDF 5.5.5、同じボード設定でコンパイル・リンク成功。Flash 1,466,042 / 2,031,616 bytes（72%）、静的RAM 66,936 bytes（20%）。生成ELFに `mbedtls_platform_set_calloc_free`・公開calloc/free・追加した割り当て関数がリンクされていることを確認した。後続の01:36ログでPSRAM有効・累積確保失敗0・generation 9でのAEC停止と録音復帰を確認。起動プローブの行は画像に含まれない。長時間の安定性と体感速度の改善は未確定。

補足: 自動停止版のビルドについて、前回は「同じコア」と記録したが、残っていた `toytalker_v07_build/build.options.json` は3.3.11を指していた。今回確認したインストール状態も3.3.11のみ。コア更新が今回の症状の原因であるかは比較していない。

参照待ち・STT補正の修正版（2026-09-10）の検証: Arduinoコア3.3.11 / IDF 5.5.5、同じ設定でコンパイル・リンク成功。Flash 1,467,162 / 2,031,616 bytes（72%）、静的RAM 66,984 bytes（20%）。`tests/aec_signal_test.cpp` は参照の補間相手が到着するまで待つ境界テストを加え全10件。`tests/stt_mic_filter_test.cpp` の5件は、ゼロ埋めとDCによる開始過渡、空入力、次の録音へのDC持越し、音声振幅の保持と丸め偏り、過大入力の飽和を確認。これらと既存のchunked受信・音量判定テストがXtensaの `-std=c++17 -Wall -Wextra -Werror -fsyntax-only` で通過。実際の音声での効果と並列実行の安定性は未確認。

Soniox先行接続分離版（2026-09-10）の検証: Arduinoコア3.3.11 / IDF 5.5.5、同じ設定で最終ソースのコンパイル・リンク成功。Flash 1,469,270 / 2,031,616 bytes（72%）、静的RAM 67,032 bytes（20%）。新タスクの8KBスタック等は動的確保で、この静的RAM値には含まれない。生成ELFにワーカーを確認。既存のAEC参照・介入判定・chunked受信・音量判定・STT補正のコンパイル時テストが通過した。WebSocketの呼び出し箇所を点検し、接続中の参照・送信・再初期化・切断を所有権で隔離し、失敗・キャンセル・5秒後も接続中の場合に使用中ソケットを破棄しないことをコードで確認した。後続の13:19に本文開始の体感改善とAEC停止後の録音復帰を実機確認。失敗時の復帰・正確な短縮量・新ワーカーのスタック余裕は未確認。

誤検出保護版（2026-09-10）の検証: Arduinoコア3.3.11 / IDF 5.5.5、同じ設定で最終ソースのコンパイル・リンク成功。Flash 1,470,122 / 2,031,616 bytes（72%）、静的RAM 67,096 bytes（20%、保存点から64 bytes増）。AEC参照・ゲートのコンパイル時テストは14件で通過。新規4件は、強く抑制された出力の却下と後続音声の再判定、25%境界・窓全体のエネルギー・64bit演算、飽和再発と古い音声で保護を短縮しないこと、次ターンの初期化を確認した。既存のchunked受信・音量判定・STT補正テストも同時に通過。13:19の発火フレームを繰り返す合成窓は使ったが、実際の4フレームや音声を再現したテストではない。誤停止防止と通常の声への反応は実機試験待ち。

AEC本体再初期化版（2026-09-10 18:26の結果を受けた変更）の検証: Arduinoコア3.3.11 / IDF 5.5.5、同じ設定でコンパイル・リンク成功。Flash 1,470,646 / 2,031,616 bytes（72%）、静的RAM 67,096 bytes（20%）。既存のAEC参照/ゲート14件・chunked受信・音量判定・STT補正のコンパイル時テストは通過。呼び出し経路を確認し、監視タスク停止後・次の通知前に本体を再作成し、失敗時は計測のみで次ターン再試行する。後続の18:43に声による停止・再生音で停止しないことの改善報告と、10ターン目の停止後の録音復帰を確認。実際のAEC学習・再確保の耐久性・初期化所要時間は未確定。

v0.5・v0.6のファームはAEC/TLSと今回の遅延対応では変更していない。18:43の改善報告を受けて保存し、本文開始の待ち・再学習・準備時間・長時間のメモリ推移を残課題とする。
