tomonoriyamazaki/toytalker/docs/esp32-aec-gate-ac-2026-09-12.md

# Cartesia・音量維持での割り込み判定比較

ユーザー指定：サービスの再生音量を下げず、音声割り込みON、Cartesiaを基準に調整する。ボタン即時停止も維持。

## 今回の到達点・一区切り（2026-09-12）

AC RMS版の実機試験で、ユーザーから「だいぶ途中で止まらなくなった」「結構近づかないと反応しなくなった」と報告。誤停止の減少は聴取による定性的な評価であり、誤停止率や反応距離は未測定。全ての誤停止が解消したとは扱わない。

ユーザーは現設定を当面の基準として受け入れ、今回の調整を一旦終了する方針。Cartesia・サービス音量維持・音声割り込みON・ボタン即時停止ON・AGGR・入力divisor=1・AC RMS閾値1200・保持128msを維持する。追加の感度変更やスマホ設定機能の実装は今回行わない。

## 重要：現在のトレードオフはAECの最終的な限界ではない

現状の判定方式のまま感度を上げると、小さい声や離れた声に反応しやすくなる一方、再生音の消し残りによる誤停止リスクも増える。ただし、調整可能な箇所が感度だけになったわけではない。**AECそのものの品質と後段の判定処理には、まだ検証すべき改善候補がある。両立できる範囲が広がる可能性はあるが、改善幅や実現を確認したわけではない。**

今回のAC RMS変更はAEC後の判定用計測の変更であり、AEC本体のエコー除去性能を向上させた証拠ではない。今後再開する場合は、以下を切り分けて検証する。

- AECへ渡す参照音とマイク音の時刻整列・実際の音響遅延。現在の16ms先行値が最適かは未検証。
- 入力の飽和、DC/低周波成分、スピーカーやマイク経路の歪み。再生音量を下げる運用を前提にせず、入力経路や前処理の改善余地を調べる。以前の入力1/4実験は改善策として採用していない。
- AECのフィルタ設定、NLPの抑制と本人の声の保持、再学習や音の切れ目での挙動。
- AEC後の判定。音量だけの判定に加え、人の声と消し残りを区別する方法の費用・遅延・精度を評価する。

再開時は固定したCartesia音声・同じ再生音量・実使用配置を基準に、無発声時の誤停止と、所定の距離/声量での割り込み成功率・反応時間を両方測る。参照/マイク/AEC出力の比較が必要で、現状のログだけで各原因を確定しない。

スマホの「音声割り込みON/OFF」「感度：低・標準・高」は今後の操作機能候補。AEC品質改善とは別で、各段階の値は実機検証が必要。アプリ・設定API・ファームの同期は未実装。[設定同期の相談記録](esp32-ota-settings-plan.md)を参照。

## 調査結果

ON復帰後turn=3「博多はどうかな。」でcause=aec_level。判定窓のmic/out RMSは2004/2092、1954/2038、1932/1994、1881/1970。最後の参照RMSは0、参照欠落・クロックリセットは0。クリップ6,334サンプル。音声受信完了前にローカル判定でキャンセル。参照0だけで実際の無音と断定しない（参照は16ms先行）。

参照はI2S送信完了コールバックでauto-clear前の音を取得する。文間400msもI2Sにゼロを書き、同じ参照経路を通る。欠落をゼロ扱いするコードではない。現ログから参照のタイミング不良は確定できない。

入力DC追従は1/1024で、AEC出力の判定は平均値を含むRMS。停止直前の緩やかな減衰は残留DC/低周波の可能性があるが、波形平均のログがなく未確定。今回の比較で確認する。

## 比較変更

`AecGateEnergy.h`で512サンプルの平均を除いたエネルギー `sum(x*x)-sum(x)^2/N` を計算。マイクとAEC出力の両方について、このAC RMSを既存ゲートへ渡す。総RMS・抑制統計は従来値を保持する。参照の時刻・PCM・スピーカー音量・AEC入力ゲイン・閾値1200・保持128ms・クリップ保護は維持。32msフレームの平均除去で低周波成分の扱いも変わるため、実際の声での反応確認が必要。人の声を識別する機能ではなく、全ての誤停止を防ぐ保証はない。

`[AEC_GATE_AC]`に総RMS、AC RMS、平均値と、総RMSなら閾値以上だがAC RMSでは未満だったフレーム数を出す。停止候補とターン終了時に記録。`AEC_GATE_FRAME`とwindow_retained_pctは今回からAC基準、`AEC_LEVEL`は従来の総RMSなので混同しない。

## 検証・実機確認

`tests/aec_gate_energy_test.cpp`のコンパイル時試験で、一定値のエネルギー除去、DCを重ねた交流波形の不変性、int16境界、既存ゲートの128ms判定を確認。実際の音声・残響の試験ではない。

ビルド先 `$env:TEMP/toytalker_v07_gate_ac_aggr`、AGGR指定 `compiler.cpp.extra_flags=-DTOYTALKER_AEC_NLP_LEVEL=1`。不調時は `$env:TEMP/toytalker_v07_voice_on_aggr` へ復旧できる。

実機では同じ音量・声で長い返答を無発声で聞き、最後までの再生を確認。その後、普段の声で「ちょっと待って」で割り込み、ボタン停止も確認する。

21:56にビルド成功（Flash 1,477,042 bytes / 静的RAM 67,144 bytes）、COM12書き込みとハッシュ検証を完了。Wi-Fi/Soniox接続、STT送信fail=0を確認。同じログ `.local/serial-logs/COM12-20260912-141828.log` へ21:56:11〜22:26:11で取得再開。聴取と実際の声への反応は未確認。
