tomonoriyamazaki/toytalker/docs/esp32-aec-input-headroom-2026-09-12.md

# AEC入力クリップの比較修正（2026-09-12）

21:03の「とりあえず長く話してみて」へのCartesia応答は、2番目のPCMフレーム受信中に `cause=aec_level` で停止。本文の続きは届いていた。AEC用マイク変換のclips=7,043 / clip_frames=64、missing/mic_drop/ref_drop/clock_resets=0。NLPはAGGR。止まる直前の候補窓はout=1,933/1,880/1,837/1,482で、最後のフレームはref=0。音源・クリップの原因・内部残響の時間は未確定だが、AEC入力の数値上の飽和は確認できる。

## 比較変更

旧変換はraw >> 14からDCを除去し、そのままint16へ飽和させていた。符号付き32bit全域を16bitへ収める変換よりゲインが高く、マイク入力が大きいとAECへ渡す前に波形が頭打ちになる。

`AecMicHeadroom.h` でDC除去後の32bit値を4で割ってからint16へ変換。すでに飽和した波形を小さくするのではなく、飽和前の値に余裕を持たせる。AEC前後のRMSを4倍してゲートと音量ログへ戻し、固定閾値を実質的に4倍へ上げることは避ける。ただしAEC/NLP内部の動作は絶対振幅にも依存し得るため、音響的な等価性や声の感度維持を保証するものではない。

参照音、再生音量、STT用マイク変換、NLP=AGGR、割り込みRMS 1,200/128ms、クリップ後の保護256ms、即時ボタン消音は維持。入力の過大値そのものを解消したとは主張しない。参照時刻やDC除去処理も今回同時に変えない。

`[AEC_INPUT] divisor=4 gate_rms_multiplier=4` で設定確認。`pre_scale_clips` は旧ゲインなら飽和するサンプル数、`actual_clips` は今回AECへ渡す値で実際に飽和したサンプル数。従来の `[AEC_STATS] clips` もactual側。クリップ保護にはactual側を渡すので、保護に頼っていた誤停止が増える可能性もあり、実機で効果を確認する。

## 確認方法

- 同じCartesiaの声・音量・配置で無発声の長めの返答を聞く。actual_clipsの減少と誤停止の有無を確認。
- 普段の声で「ちょっと待って」と言い、声の反応が保たれるか確認。
- ボタン短押しと通常の録音復帰を確認。
- 不調なら前の `$env:TEMP/toytalker_v07_button_aggr` を書き戻す。

固定音声再生ではないため予備比較。旧ログだけから、入力ゲイン変更で必ず改善すると断定できない。

## 検証

`tests/aec_mic_headroom_test.cpp` で飽和前スケーリング、正負境界、極端値の安全な飽和、ゲート音量単位をC++17 static_assertで検証。既存AEC参照/ゲートとstream completionのテストも成功。

比較ビルド先は `$env:TEMP/toytalker_v07_headroom_aggr`。FQBNは従来と同じ、`compiler.cpp.extra_flags=-DTOYTALKER_AEC_NLP_LEVEL=1`。

Arduino ESP32 3.3.11でビルド成功（Flash 1,476,542 bytes、静的RAM 67,128 bytes）。21:08台にCOM12（ESP32-S3、MAC 90:da:72:49:ba:e4）へ書き込み、ハッシュ検証と再起動後のWi-Fi/Soniox接続・STT送信を確認。入力クリップと誤停止への実機効果は未確認。

ログは `.local/serial-logs/COM12-20260912-141828.log` へ追記、今回の受信は21:08:41〜21:38:41の予定。書き込みのため前の受信を終了してから再開した。

## 21:16 実機結果：途中停止は残る

「なんか適当に、昔話とかしてみて。」へのCartesia応答（再起動後turn=2）は2番目のPCM受信中にcause=aec_levelで停止。ユーザーも途中停止を報告。`pre_scale_clips=11843 actual_clips=258`。同じ入力について旧ゲインで飽和し得たサンプルの約97.8%は新変換で飽和しなくなったが、飽和は残り、誤停止対策として十分ではなかった。前回と同じ波形ではないため、前回の7,043との直接的な改善率にはしない。

候補窓出力（旧単位換算）1,812/8,132/11,684/5,680、出力/入力比27.3%。入力ピーク86,640、全体抑制4.6dB、missing/mic_drop/ref_drop/clock_resets=0。入力を縮小しても残留成分が停止条件を満たす。ここから追加のゲイン縮小や閾値上げを成功策と断定しない。実際の入力振幅・音響配置/音量・参照整列の切り分けが必要。比較版は採用確定せず、そのまま保持し追加書き込みはしていない。

## 21:29 入力縮小前へ書き戻し

ユーザーがバリバリ音の悪化を感じると報告。入力縮小との因果は未確定。比較の承認を受け、保存済み `$env:TEMP/toytalker_v07_button_aggr` をCOM12へ書き戻し、ハッシュ検証・再起動後のSTT送信を確認した。AGGRとボタン即時消音、stream completion修正は含むが、入力1/4縮小は含まない。

作業ツリーの入力縮小比較コードは調査用に残しているため、実機の版と一致しない。保存済みbutton_aggrバイナリを再生成せず使用した。同じ声・音量でのバリバリ音と途中停止の比較結果は未確認。

同じログファイルへ追記受信を再開、21:29:44〜21:59:44の予定。

## 21:37 自動割り込み停止を無効にする比較

入力縮小前へ復旧後のturn=6で、ユーザーが最後の一文の欠落を報告。「あなた様は、どのようなものがお好きですか？」のPCM 113,520 bytesを全量受信し、done=1 / http_complete=1 / failed=0。その約3.3秒後、残りの再生中にAEC_TRIGGER、cause=aec_level、interrupted=1、DMA flush未完了。履歴の全文保存は聴取完了を保証しない。

ユーザーの依頼で `AEC_BARGE_DETECT_ONLY=true` に変更。AEC計測は継続するが、その判定ではアンプ停止・再生キャンセルをしない。生マイクのフォールバックも従来どおり計測のみ。ボタン即時停止は維持。

21:38にビルド成功（Flash 1,476,382 bytes / 静的RAM 67,128 bytes）、COM12へ書き込み・ハッシュ検証済み。起動ログの `aec_detect_only=1`、Soniox接続とSTT送信fail=0を確認。聴取確認はこれから。同じログへの取得を21:38:49〜22:08:49で再開した。

入力縮小を再導入しないよう `TOYTALKER_AEC_MIC_DIVISOR` を追加し、既定値を1（縮小なし）へ戻した。4を指定すると以前の縮小実験になる。数値テストは1/4の両設定でコンパイル成功。AGGRビルドは `compiler.cpp.extra_flags=-DTOYTALKER_AEC_NLP_LEVEL=1`、保存先 `$env:TEMP/toytalker_v07_detect_only_aggr`。長めの応答の最終文までの再生と、ボタン停止を実機で比較する。

## OFF比較の結果とONへの復帰

2026-09-12 21:48にビルド成功（Flash 1,476,506 bytes、静的RAM 67,128 bytes）、COM12へ書き込み・ハッシュ検証済み。起動ログのaec_detect_only=0、Soniox接続とSTT送信fail=0を確認。同じログファイルへの取得を21:48:59〜22:18:59で再開。誤停止を解消した変更ではなく、ユーザー指定の調整基準への復帰。

ユーザーが自動割り込みOFFで「最後まで読まれる」「ボタン押したら止まる」と確認。その後、音声割り込みをONで継続し、Cartesiaを基準に調整する方針を指定。`AEC_BARGE_DETECT_ONLY=false` に戻す。AGGR・入力divisor=1・既存閾値・ボタン即時停止は維持し、今回新たな閾値調整はしない。ビルド先は `$env:TEMP/toytalker_v07_voice_on_aggr`。OFF比較版は前記の保存先に保持する。
